zmk5566/Hexblocks/frontend/bridge/serial_bridge.py

#!/usr/bin/env python3
"""WearBlocks Serial-to-WebSocket bridge.

Reads $-prefixed lines from ESP32 hub serial, broadcasts JSON over WebSocket.

Usage:
  python serial_bridge.py /dev/cu.usbmodem14101   # real hardware
  python serial_bridge.py --mock                   # single IMU simulator
  python serial_bridge.py --sim                    # interactive multi-module simulator
  python serial_bridge.py --sim-demo               # auto-load demo (HR stacked on IMU)
"""
import argparse, asyncio, base64, copy, json, math, os, random, re, sys, time, threading
from collections import deque
from datetime import datetime
from functools import partial
from http.server import SimpleHTTPRequestHandler, HTTPServer
from pathlib import Path

import serial
import websockets

from wb_eca import ECAEngine, Act, ActionMode, CH, Action as EcaAction
from logger_profile import (
    MAX_SUBSCRIPTIONS as LOGGER_MAX_SUBSCRIPTIONS,
    MODES as LOGGER_MODES,
    RECORD_TYPES as LOGGER_RECORD_TYPES,
    default_config_rev as logger_default_config_rev,
    decode_profile as decode_logger_profile,
    encode_profile_base64,
)
from wb_protocol import parse_line as _parse_wire
import serial_io
from transport import (
    Transport, SerialTransport, BleTransport, ble_scan as ble_scan_devices,
)
from osc_forwarder import (
    OscForwarder, schema_to_default_mappings, load_channel_catalog,
)
from osc_ingress import OscIngress, ControlRequest

WS_PORT, HTTP_PORT, BAUD = 8765, 3000, 115200

PAIRED_DEVICES_PATH = Path(__file__).parent / "paired_devices.json"


def _load_paired() -> list[dict]:
    """Return list of {address, name, last_seen, auto_reconnect}."""
    try:
        if PAIRED_DEVICES_PATH.exists():
            data = json.loads(PAIRED_DEVICES_PATH.read_text())
            if isinstance(data, list):
                return data
    except Exception as e:
        print(f"[bridge] failed to load paired devices: {e!r}")
    return []


def _save_paired(devices: list[dict]) -> None:
    try:
        PAIRED_DEVICES_PATH.write_text(json.dumps(devices, indent=2))
    except Exception as e:
        print(f"[bridge] failed to save paired devices: {e!r}")


def _upsert_paired(address: str, name: str, *, auto_reconnect: bool | None = None):
    devs = _load_paired()
    now = int(time.time())
    found = None
    for d in devs:
        if d.get("address") == address:
            found = d
            break
    if found is None:
        found = {"address": address, "name": name,
                 "last_seen": now, "auto_reconnect": False}
        devs.append(found)
    else:
        found["name"] = name or found.get("name", "")
        found["last_seen"] = now
    if auto_reconnect is not None:
        found["auto_reconnect"] = bool(auto_reconnect)
    _save_paired(devs)
    return found


def _forget_paired(address: str) -> bool:
    devs = _load_paired()
    new = [d for d in devs if d.get("address") != address]
    if len(new) == len(devs):
        return False
    _save_paired(new)
    return True


# ── Debug recorder ───────────────────────────────────────────────
# When `--log <path>` is passed, every serial line in/out, every parsed
# event, and every WS-inbound command is appended to the file with an
# ISO timestamp and a one-letter direction tag:
#   RX  hub → bridge (raw serial line, with or without $)
#   TX  bridge → hub (write queue commands)
#   EV  parsed event broadcast to WS clients
#   WS  WS client → bridge inbound JSON
#   ..  bridge diagnostics (transport connect/drop, reset markers)
# Writes are flushed per line so an unclean shutdown still leaves a
# usable trail.
class LogRecorder:
    def __init__(self, path: str | None):
        self._fh = None
        if path:
            self._fh = open(path, "a", buffering=1, encoding="utf-8")
            self._write("--", f"--- bridge start pid={__import__('os').getpid()} ---")

    def _write(self, tag: str, text: str):
        if self._fh is None:
            return
        try:
            ts = datetime.now().isoformat(timespec="milliseconds")
            self._fh.write(f"{ts} {tag} {text}\n")
        except Exception:
            pass  # never let logging crash the bridge

    def rx(self, line: str):
        self._write("RX", line.rstrip("\r\n"))

    def tx(self, line: str):
        self._write("TX", line.rstrip("\r\n"))

    def event(self, msg: dict):
        try:
            self._write("EV", json.dumps(msg, ensure_ascii=False))
        except Exception:
            self._write("EV", repr(msg))

    def ws(self, raw: str):
        self._write("WS", raw if isinstance(raw, str) else repr(raw))

    def note(self, text: str):
        self._write("..", text)

    def close(self):
        if self._fh is not None:
            try:
                self._fh.close()
            except Exception:
                pass


recorder = LogRecorder(None)  # replaced in main() if --log given

HUB_RESET_MARKERS = (
    "WearBlocks Hub",
    "ESP-ROM",
    "rst:",
    "boot:",
    "Brownout",
    "Guru Meditation",
    "Rebooting",
)
HUB_READY_MARKERS = (
    "[WAIT] Listening for HELLO",
    "[WAIT] Listening for module HELLO",
)


def _classify_debug_line(line: str) -> str | None:
    """Return a compact diagnostic tag for notable hub debug output."""
    if any(marker in line for marker in HUB_RESET_MARKERS):
        return "hub_reset_marker"
    if any(marker in line for marker in HUB_READY_MARKERS):
        return "hub_ready_marker"
    return None

DEFAULT_MODULE_COLOR = "#888888"
COLOR_MAP = {
    "imu": "#7CA1BB", "imuv": "#7CA1BB",
    "motion_sensing": "#7CA1BB", "acc": "#7CA1BB",
    "acceleration": "#7CA1BB", "accelerometer": "#7CA1BB",
    "hr": "#7B68EE", "spo": "#7B68EE",
    "biometric": "#7B68EE", "heart": "#7B68EE",
    "tmp": "#F5A623", "temp": "#F5A623", "bme": "#F5A623",
    "environmental": "#F5A623",
    "vib": "#50C878", "vibration": "#50C878",
    "haptic": "#50C878", "haptic_output": "#50C878",
    "led": "#C68E9E", "visual_output": "#C68E9E",
    "rgb": "#C68E9E", "neopixel": "#C68E9E",
    "light": "#C1B496", "light_sensing": "#C1B496",
    "audio": "#9885BF", "audio_output": "#9885BF",
    "audio_synth": "#9885BF", "amp": "#9885BF",
    "amplifier": "#9885BF", "speaker": "#9885BF",
    "tone": "#9885BF", "tone_generation": "#9885BF",
    "tone_generator": "#9885BF",
    "wireless_uplink": "#4FA7A1", "logger": "#4FA7A1",
    "lora": "#4FA7A1", "loralog": "#4FA7A1",
    "lora_uplink": "#4FA7A1", "batch_log": "#4FA7A1",
    "motor": "#D97757", "dual_motor": "#D97757",
    "motor_output": "#D97757",
    "knob": "#98AF6F", "rotary": "#98AF6F",
    "input_control": "#98AF6F", "pot": "#98AF6F",
    "hub": "#989898",
}
COLOR_PREFIXES = (
    "imu", "acc", "hr", "spo", "tmp", "temp", "bme",
    "vib", "led", "light", "audio", "amp", "knob", "hub",
    "lora", "logger", "motor",
)

# Category → sensor type shorthand (for WebSocket "sensor" field)
CAT_MAP = {
    "motion_sensing": "imu",
    "biometric":      "hr",
    "environmental":  "temp",
    "visual_output":  "led",
    "haptic_output":  "vibration",
    "light_sensing":  "light",
    "audio_output":   "audio",
    "wireless_uplink": "logger",
    "motor_output":   "motor",
}

clients: set = set()

# ── Identity model ────────────────────────────────────────────────
# The hub's v2 wire protocol is UID-keyed: every $H/$D/$I/$S/$X/$U/$F/$C/$c/$T
# line carries the module's 8-hex-char UID. Slot is a hub-internal concept;
# it never appears on the wire after the v2 refactor. The bridge therefore
# keys all caches by UID. The sim modes (which still need slot for the ECA
# engine's action dispatch) keep their own slot-keyed bookkeeping via the
# uid_by_slot / slot_by_uid side indexes.

# UID-keyed caches (populated by parse_line from real hardware and, after
# commit 3, by the sim's synthetic-UID broadcast path).
modules_by_uid: dict = {}           # uid → mod_id
module_types_by_uid: dict = {}      # uid → sensor type shorthand
msg_cache_by_uid: dict = {}         # uid → {"hello": msg, "descriptor": msg}
link_cache_by_uid: dict = {}        # uid → latest link_state msg
# Stack relationships keyed by parent UID + face.
stack_cache_by_uid: dict = {}       # (parent_uid, parent_face) → child_stack msg
# Latest actuator state per uid (LED + vib).
actuator_cache_by_uid: dict = {}    # uid → actuator_state msg
logger_status_by_uid: dict = {}     # uid → latest logger_status msg
logger_config_by_uid: dict = {}     # uid → latest bridge-sent logger_config msg

# `$Q,DONE` is intentionally compact on the firmware wire, so the bridge tracks
# the outbound query commands that are known to terminate with DONE and annotates
# the inbound JSON event with `command`. This lets browser clients distinguish an
# empty TOPO snapshot from a STATUS/ECA completion with no topology rows.
QUERY_DONE_COMMANDS = {"STATUS", "TOPO", "ECA"}
pending_query_done_commands: deque[str] = deque()
topo_snapshot_uids: set[str] = set()
WIRELESS_TRANSPORT_MODES = {
    "can_only",
    "wifi_only",
    "can_primary_wifi_fallback",
    "wifi_primary_can_fallback",
    "dual_send_debug",
}

# Side indexes for sim / ECA dispatch — slot is CAN-bus addressing concept,
# not exposed on the v2 wire. Populated by sim in commit 3.
uid_by_slot: dict = {}              # slot → uid (sim authoritative)
slot_by_uid: dict = {}              # uid → slot (sim authoritative)

# Legacy slot-keyed caches — retained only so the existing sim path keeps
# working during this transitional commit. Commit 3 removes these by
# migrating the sim to emit uid-keyed frames via the _by_uid dicts above.
modules: dict = {}
module_types: dict = {}
msg_cache: dict = {}
stack_cache: dict = {}
actuator_cache: dict = {}

serial_write_queue: asyncio.Queue = asyncio.Queue()

# Request-ID-bearing OSC controls waiting for a Hub/simulator result. The
# actual UDP socket lives in ``osc_ingress``; keeping lifecycle state here lets
# normal parsed bridge events close the loop without coupling wb_protocol.py to
# networking.
osc_ingress: OscIngress | None = None
osc_control_pending: dict[str, dict] = {}
OSC_CONTROL_ROUTE_TIMEOUT_S = 3.0
OSC_CONTROL_RETENTION_S = 10.0

# ── Active transport (USB or BLE — mutually exclusive) ─────────
# Set by serial_loop / ble_loop. The transport_supervisor coroutine
# watches `transport_request` for switch commands from WS clients.
current_transport: Transport | None = None
transport_request: asyncio.Queue = asyncio.Queue()
# Cached for the next client that connects so the UI can render the
# current transport without a fresh status push.
last_transport_status: dict = {"type": "transport_status",
                                "transport": None, "address": None,
                                "label": None, "connected": False}

# Latest ECA status + bytecode from the hub. Cached so a freshly-
# connected WS client gets a full snapshot without waiting for the
# next $Q,ECA round-trip.
last_eca_status:   dict | None = None
last_eca_bytecode: dict | None = None


def clear_hub_runtime_state() -> None:
    """Discard identities and replay caches owned by a disconnected Hub."""
    global last_eca_status, last_eca_bytecode
    for cache in (
        modules_by_uid, module_types_by_uid, msg_cache_by_uid,
        stack_cache_by_uid, actuator_cache_by_uid,
        uid_by_slot, slot_by_uid,
        modules, module_types, msg_cache, stack_cache, actuator_cache,
    ):
        cache.clear()
    pending_query_done_commands.clear()
    topo_snapshot_uids.clear()
    last_eca_status = None
    last_eca_bytecode = None
    for request_id in list(osc_control_pending):
        if osc_ingress is not None:
            osc_ingress.result(request_id, ok=False, stage="transport",
                               detail="Hub transport disconnected")
        _finish_osc_control(request_id)

# ── ECA engine (used in --sim modes only) ──────────────────────
# Per-module-type mapping from simulator data field name → ECA channel id.
# Field names should match the channel catalog labels so legacy batched
# simulator payloads do not surface fake axis names in the frontend.
SIM_CHANNEL_MAP = {
    "imu":  {"ax": CH.AX, "ay": CH.AY, "az": CH.AZ,
             "gx": CH.GX, "gy": CH.GY, "gz": CH.GZ},
    "hr":   {"bpm": CH.BPM, "spo2": CH.SPO2},
    "temp": {"celsius": CH.CELSIUS, "humidity": CH.HUMIDITY},
    "knob": {"knob": CH.KNOB},
    "light": {"light": CH.LIGHT},
}


def _sim_monotonic_ms() -> int:
    """Monotonic clock for simulator scheduling; wall-clock jumps are irrelevant."""
    return time.monotonic_ns() // 1_000_000

# One global engine. The on_action callback is set later (after dispatch_action
# is defined) to avoid forward-reference noise.
eca = ECAEngine()

# Embedded OSC forwarder (Mode B: hub → bridge → UDP/OSC sink). Started in
# main() so it binds to the running asyncio loop. forward(msg) is called
# from broadcast(); see osc_forwarder.py for queue + drop-oldest design.
# `allow_remote` is patched in main() from the CLI flag before start().
osc_forwarder = OscForwarder()


async def _enqueue_osc_control(request: ControlRequest) -> None:
    osc_control_pending[request.request_id] = {
        "request": request,
        "queued_at": time.monotonic(),
        "routed_at": None,
        "state_seen": False,
    }
    await serial_write_queue.put(request.serial_line)
    print(f"[bridge] OSC→serial: $AO {request.request_id} "
          f"{request.uid} {request.cmd} (<{len(request.wire_params)} bytes>)")


def create_osc_ingress(
    host: str = "127.0.0.1",
    port: int = 7001,
    *,
    allow_remote: bool = False,
) -> OscIngress:
    """Create the OSC control listener on the shared command queue seam."""
    return OscIngress(
        host=host,
        port=port,
        allow_remote=allow_remote,
        known_uids=lambda: modules_by_uid.keys(),
        enqueue=_enqueue_osc_control,
        on_error=lambda message: print(f"[osc-in] rejected: {message}"),
    )


def _finish_osc_control(request_id: str) -> None:
    osc_control_pending.pop(request_id, None)
    if osc_ingress is not None:
        osc_ingress.forget(request_id)


def _handle_osc_bridge_event(msg: dict) -> None:
    """Translate normal bridge events into unicast OSC control replies."""
    if osc_ingress is None:
        return
    mtype = msg.get("type")

    if mtype == "command_ack":
        # Hub/sim replies: "$OK AO <request_id> ..." / "$ERR AO ...".
        match = re.match(r"^AO\s+([A-Za-z0-9_.:-]{1,64})(?:\s|$)",
                         str(msg.get("text", "")))
        if not match:
            return
        request_id = match.group(1)
        pending = osc_control_pending.get(request_id)
        if pending is None:
            return
        ok = msg.get("status") == "ok"
        osc_ingress.result(
            request_id, ok=ok, stage="routed" if ok else "route",
            detail=str(msg.get("text", "")))
        if ok:
            pending["routed_at"] = time.monotonic()
            if pending.get("state_seen") and "route=local" in str(msg.get("text", "")):
                osc_ingress.result(request_id, ok=True, stage="applied",
                                   detail="local actuator executed")
                _finish_osc_control(request_id)
        else:
            _finish_osc_control(request_id)
        return

    if mtype == "actuator_state":
        request_id = str(msg.get("request_id") or "")
        if not request_id or request_id not in osc_control_pending:
            return
        pending = osc_control_pending[request_id]
        pending["state_seen"] = True
        osc_ingress.state(request_id, msg)
        if msg.get("confirmed"):
            osc_ingress.result(request_id, ok=True, stage="applied",
                               detail="actuator state confirmed")
            _finish_osc_control(request_id)
        return

    if mtype == "wireless_command_result":
        request_id = str(msg.get("request_id") or "")
        if not request_id or request_id not in osc_control_pending:
            return
        ok = msg.get("status") == "ack"
        osc_ingress.result(
            request_id, ok=ok, stage="applied" if ok else "module",
            detail=str(msg.get("detail", "")))
        _finish_osc_control(request_id)


async def _osc_control_timeout_loop() -> None:
    while True:
        await asyncio.sleep(0.25)
        now = time.monotonic()
        for request_id, pending in list(osc_control_pending.items()):
            routed_at = pending.get("routed_at")
            if routed_at is None:
                if now - pending["queued_at"] >= OSC_CONTROL_ROUTE_TIMEOUT_S:
                    if osc_ingress is not None:
                        osc_ingress.result(request_id, ok=False, stage="route",
                                           detail="Hub response timeout")
                    _finish_osc_control(request_id)
            elif now - routed_at >= OSC_CONTROL_RETENTION_S:
                # CAN currently has no module-level action ACK. A routed ACK
                # plus commanded state is the strongest honest result there;
                # retain briefly for late state, then release bookkeeping.
                _finish_osc_control(request_id)


def _is_hex_color(value) -> bool:
    if not isinstance(value, str):
        return False
    value = value.strip()
    return (
        len(value) == 7
        and value.startswith("#")
        and all(ch in "0123456789abcdefABCDEF" for ch in value[1:])
    )


def _color_tokens(value):
    raw = str(value or "").strip().lower()
    if not raw:
        return
    normalized = re.sub(r"[^a-z0-9]+", "_", raw).strip("_")
    if not normalized:
        return
    yield normalized
    for part in normalized.split("_"):
        if not part:
            continue
        yield part
        prefix = re.match(r"[a-z]+", part)
        if prefix:
            yield prefix.group(0)


def _descriptor_color(desc: dict | None) -> str | None:
    if not isinstance(desc, dict):
        return None
    if _is_hex_color(desc.get("color")):
        return desc["color"].strip()
    signals = [
        desc.get("id"),
        desc.get("moduleId"),
        desc.get("name"),
        desc.get("type"),
        desc.get("cat"),
        desc.get("category"),
    ]
    for cap in desc.get("caps", []) or []:
        if not isinstance(cap, dict):
            continue
        signals.extend([
            cap.get("m"),
            cap.get("modality"),
            cap.get("t"),
            cap.get("type"),
        ])
    color = color_for(*signals)
    return None if color == DEFAULT_MODULE_COLOR else color


def color_for(*signals) -> str:
    for signal in signals:
        for token in _color_tokens(signal) or ():
            if token in COLOR_MAP:
                return COLOR_MAP[token]
            for prefix in COLOR_PREFIXES:
                if token.startswith(prefix):
                    return COLOR_MAP[prefix]
    return DEFAULT_MODULE_COLOR


def _descriptor_tokens(desc: dict | None) -> set[str]:
    tokens = set()

    def add(value):
        for token in _color_tokens(value) or ():
            tokens.add(token)

    if not isinstance(desc, dict):
        return tokens
    for key in ("id", "moduleId", "name", "type", "cat", "category"):
        add(desc.get(key))
    for cap in desc.get("caps", []) or []:
        if not isinstance(cap, dict):
            continue
        for key in ("t", "type", "m", "modality"):
            add(cap.get(key))
    return tokens


def _module_is_logger_uid(uid: str) -> bool:
    uid = str(uid or "").strip().upper()
    desc = msg_cache_by_uid.get(uid, {}).get("descriptor", {}).get("data")
    if not desc:
        slot = slot_by_uid.get(uid)
        sim_mod = sim_modules.get(slot) if slot is not None else None
        if sim_mod is not None:
            desc = sim_mod.descriptor
    tokens = _descriptor_tokens(desc)
    mod_id = modules_by_uid.get(uid, "")
    tokens.update(_color_tokens(mod_id) or [])
    return bool({
        "loralogv1", "loralog", "logger", "wireless_uplink",
        "lora_uplink", "batch_log",
    } & tokens)


def _catalog_channel_ids_for_type(sensor_type: str) -> set[int]:
    try:
        catalog = load_channel_catalog(CHANNEL_CATALOG_PATH)
    except Exception:
        return set()
    channels = catalog.get("channels", {})
    names = catalog.get("sensor_capabilities", {}).get(sensor_type, []) or []
    out = set()
    for name in names:
        entry = channels.get(name)
        if isinstance(entry, dict) and isinstance(entry.get("id"), int):
            out.add(int(entry["id"]))
    return out


def _channel_ids_for_uid(uid: str) -> set[int]:
    uid = str(uid or "").strip().upper()
    desc = msg_cache_by_uid.get(uid, {}).get("descriptor", {}).get("data")
    tokens = _descriptor_tokens(desc)
    sensor_type = module_types_by_uid.get(uid)
    if sensor_type:
        tokens.add(sensor_type)
    ids = set()
    for token in tokens:
        ids.update(_catalog_channel_ids_for_type(token))
    return ids


def _validate_logger_subscriptions(raw_subs, logger_uid: str) -> list[dict]:
    if not isinstance(raw_subs, list):
        raise ValueError("subscriptions must be a list")
    if len(raw_subs) > LOGGER_MAX_SUBSCRIPTIONS:
        raise ValueError(f"too many subscriptions, max {LOGGER_MAX_SUBSCRIPTIONS}")

    logger_uid = str(logger_uid or "").strip().upper()
    normalized: list[dict] = []
    seen = set()
    for raw in raw_subs:
        if not isinstance(raw, dict):
            raise ValueError("subscription must be an object")
        sub = {
            "source_uid": str(raw.get("source_uid", "")).strip().upper().replace("0X", ""),
            "channel_id": int(raw.get("channel_id", 0)),
            "record_type": str(raw.get("record_type", "sensor")).strip(),
            "mode": str(raw.get("mode", "latest_interval")).strip(),
            "min_interval_ms": int(raw.get("min_interval_ms", 0)),
            "threshold": float(raw.get("threshold", 0.0)),
            "flags": int(raw.get("flags", 0)),
        }
        if sub["record_type"] not in LOGGER_RECORD_TYPES:
            raise ValueError(f"bad record_type {sub['record_type']!r}")
        if sub["mode"] not in LOGGER_MODES:
            raise ValueError(f"bad logger mode {sub['mode']!r}")
        if not re.fullmatch(r"[0-9A-F]{8}", sub["source_uid"]):
            raise ValueError(f"bad source_uid {sub['source_uid']!r}")
        if sub["source_uid"] == logger_uid:
            raise ValueError("logger cannot subscribe to itself")
        if sub["source_uid"] not in modules_by_uid:
            raise ValueError(f"unknown source_uid {sub['source_uid']}")
        if not 0 <= sub["channel_id"] < 48:
            raise ValueError("channel_id must be 0..47")
        if not 0 <= sub["min_interval_ms"] <= 86_400_000:
            raise ValueError("min_interval_ms out of range")
        if not math.isfinite(sub["threshold"]):
            raise ValueError("threshold must be finite")
        if not 0 <= sub["flags"] <= 255:
            raise ValueError("flags must be 0..255")
        if sub["record_type"] == "sensor":
            allowed = _channel_ids_for_uid(sub["source_uid"])
            if allowed and sub["channel_id"] not in allowed:
                raise ValueError(
                    f"channel {sub['channel_id']} is not advertised by {sub['source_uid']}"
                )
        key = (sub["source_uid"], sub["channel_id"], sub["record_type"])
        if key in seen:
            continue
        seen.add(key)
        normalized.append(sub)
    return normalized


def _track_query_command(command: str) -> None:
    cmd = str(command or "").strip().upper()
    if cmd in QUERY_DONE_COMMANDS:
        pending_query_done_commands.append(cmd)


def _clear_pending_query_state(reason: str) -> None:
    pending = len(pending_query_done_commands)
    topo_rows = len(topo_snapshot_uids)
    if not pending and not topo_rows:
        return
    pending_query_done_commands.clear()
    topo_snapshot_uids.clear()
    recorder.note(
        f"cleared pending query state ({pending} done marker(s), "
        f"{topo_rows} topo row(s)): {reason}"
    )


async def _queue_query_command(command: str) -> None:
    """Queue a hub query and remember which compact $Q,DONE it will finish."""
    cmd = str(command or "").strip().upper()
    if not cmd:
        return
    _track_query_command(cmd)
    await serial_write_queue.put(f"$Q,{cmd}\n")


def _drop_pending_query_writes(reason: str) -> int:
    """Remove stale queued $Q commands before a newly opened transport sync."""
    kept = []
    dropped = 0
    while True:
        try:
            cmd = serial_write_queue.get_nowait()
        except asyncio.QueueEmpty:
            break
        if str(cmd).lstrip().upper().startswith("$Q,"):
            dropped += 1
        else:
            kept.append(cmd)
    for cmd in kept:
        serial_write_queue.put_nowait(cmd)
    if dropped:
        _clear_pending_query_state(reason)
        recorder.note(f"dropped {dropped} queued query command(s): {reason}")
        print(f"[bridge] dropped {dropped} queued query command(s): {reason}")
    else:
        _clear_pending_query_state(reason)
    return dropped


def _consume_tracked_query_done(command: str) -> None:
    cmd = str(command or "").strip().upper()
    if pending_query_done_commands and pending_query_done_commands[0] == cmd:
        pending_query_done_commands.popleft()


def _prune_uid_caches_to(live_uids: set[str]) -> None:
    """Drop bridge replay caches for UIDs absent from an authoritative TOPO."""
    cached_uids = (set(modules_by_uid) | set(module_types_by_uid)
                   | set(msg_cache_by_uid) | set(link_cache_by_uid)
                   | set(actuator_cache_by_uid)
                   | set(logger_status_by_uid) | set(logger_config_by_uid)
                   | set(slot_by_uid))
    dead_uids = cached_uids - live_uids
    for uid in dead_uids:
        modules_by_uid.pop(uid, None)
        module_types_by_uid.pop(uid, None)
        msg_cache_by_uid.pop(uid, None)
        link_cache_by_uid.pop(uid, None)
        actuator_cache_by_uid.pop(uid, None)
        logger_status_by_uid.pop(uid, None)
        logger_config_by_uid.pop(uid, None)
        slot = slot_by_uid.pop(uid, None)
        if slot is not None:
            uid_by_slot.pop(slot, None)

    for key, stack_msg in list(stack_cache_by_uid.items()):
        parent_uid, _parent_face = key
        child_uid = stack_msg.get("child_uid")
        if parent_uid not in live_uids or (child_uid and child_uid not in live_uids):
            stack_cache_by_uid.pop(key, None)

    if dead_uids:
        print(f"[bridge] TOPO pruned stale cache: {sorted(dead_uids)}")


def _wire_u32_be(params: list[int], offset: int) -> int:
    if len(params) < offset + 4:
        return 0
    return ((params[offset] << 24) | (params[offset + 1] << 16)
            | (params[offset + 2] << 8) | params[offset + 3])


def _decode_wire_actuator_state(msg: dict) -> dict:
    """Project a Hub $AS command echo into the UI's rich actuator shape."""
    uid = msg["uid"]
    command = int(msg.get("cmd", 0))
    params = [int(value) & 0xFF for value in msg.get("params", [])]
    previous = actuator_cache_by_uid.get(uid, {})
    now_ms = int(time.time() * 1000)
    state = {
        **previous,
        **msg,
        "uid": uid,
        "slot": slot_by_uid.get(uid),
        "cmd": command,
        "params": params,
        "ts": now_ms,
        "led": copy.deepcopy(previous.get("led", {
            "r": 0, "g": 0, "b": 0, "brightness": 0,
            "mode": "off", "until_ms": 0,
        })),
        "vib": copy.deepcopy(previous.get("vib", {
            "intensity": 0, "mode": "off", "until_ms": 0,
        })),
        "audio": copy.deepcopy(previous.get("audio", {
            "frequency_hz": 0, "amplitude": 0, "mode": "off",
            "until_ms": 0,
        })),
        "motors": copy.deepcopy(previous.get("motors", {
            "1": {"mode": "stop", "speed": 0, "until_ms": 0},
            "2": {"mode": "stop", "speed": 0, "until_ms": 0},
        })),
    }

    if command in (Act.LED_OFF, Act.LED_STOP):
        state["led"] = {"r": 0, "g": 0, "b": 0, "brightness": 0,
                        "mode": "off", "until_ms": 0}
    elif command in (Act.LED_SOLID, Act.LED_RAMP, Act.LED_BREATHE,
                     Act.LED_BLINK, Act.LED_RAINBOW):
        duration = _wire_u32_be(params, 3)
        state["led"] = {
            "r": params[0] if len(params) > 0 else 0,
            "g": params[1] if len(params) > 1 else 0,
            "b": params[2] if len(params) > 2 else 0,
            "brightness": 255,
            "mode": "solid" if command == Act.LED_SOLID else "effect",
            "until_ms": now_ms + duration if duration else 0,
        }
    elif command == Act.VIBRATE:
        duration = _wire_u32_be(params, 1)
        state["vib"] = {
            "intensity": params[0] if params else 0,
            "mode": "on",
            "until_ms": now_ms + duration if duration else 0,
        }
    elif command == Act.VIBRATE_PULSE:
        on_ms = (params[1] if len(params) > 1 else 10) * 10
        off_ms = (params[2] if len(params) > 2 else 10) * 10
        count = params[3] if len(params) > 3 else 1
        duration = (on_ms + off_ms) * max(1, count)
        state["vib"] = {
            "intensity": params[0] if params else 0,
            "mode": "pulse", "on_ms": on_ms, "off_ms": off_ms,
            "count": count, "until_ms": now_ms + duration,
        }
    elif command == Act.VIBRATE_RAMP:
        duration = _wire_u32_be(params, 2)
        state["vib"] = {
            "intensity": params[1] if len(params) > 1 else 0,
            "from": params[0] if params else 0,
            "mode": "ramp",
            "until_ms": now_ms + duration if duration else 0,
        }
    elif command == Act.VIBRATE_STOP:
        state["vib"] = {"intensity": 0, "mode": "off", "until_ms": 0}
    elif command == Act.AUDIO_SET_TONE:
        frequency = (params[0] if params else 0) \
            | ((params[1] if len(params) > 1 else 0) << 8)
        duration = _wire_u32_be(params, 3)
        state["audio"] = {
            "frequency_hz": frequency,
            "amplitude": params[2] if len(params) > 2 else 0,
            "mode": "tone",
            "until_ms": now_ms + duration if duration else 0,
        }
    elif command == Act.AUDIO_STOP:
        state["audio"] = {"frequency_hz": 0, "amplitude": 0,
                          "mode": "off", "until_ms": 0}
    elif command == Act.MOTOR_SET and len(params) >= 5:
        motor = params[0]
        mode = params[1]
        duration = (params[3] << 8) | params[4]
        if motor in (1, 2):
            state["motors"][str(motor)] = {
                "mode": ("stop" if mode == 0 or params[2] == 0 else
                         "forward" if mode == 1 else "reverse"),
                "speed": params[2],
                "until_ms": now_ms + duration if duration else 0,
            }
    return state


def parse_line(raw: str):
    """Parse a $-prefixed hub line into the bridge's JSON-shaped event.

    Wire decoding is delegated to `wb_protocol.parse_line`; this wrapper
    adds bridge-layer concerns: slot crosswalk via `slot_by_uid`, color
    derivation, descriptor field normalization, the `face` back-compat
    alias, and the cache cleanup triggered by `$U`.
    """
    msg = _parse_wire(raw)
    if msg is None:
        return None
    mtype = msg["type"]

    if mtype == "hello":
        uid = msg["uid"]
        if msg["id"]:
            modules_by_uid[uid] = msg["id"]
        mod_id = msg["id"] or modules_by_uid.get(uid, "")
        cached_desc = msg_cache_by_uid.get(uid, {}).get("descriptor", {}).get("data")
        msg["id"] = mod_id
        msg["slot"] = slot_by_uid.get(uid)
        msg["color"] = _descriptor_color(cached_desc) \
            or color_for(mod_id, module_types_by_uid.get(uid))
        # Legacy `face` alias is the *hub* face the module sits on, or 0
        # for a stacked child (which has no hub face — its position is
        # described by parent_uid + parent_face, not by its own face).
        # Setting face=parent_face unconditionally would make the canvas
        # draw stacked children at hub.F<parent_face> for the brief
        # window between cache replay and TOPO reconcile, which looks
        # exactly like an orphan module.
        msg["face"] = msg["parent_face"] if msg["parent_is_hub"] else 0
        cached_link = link_cache_by_uid.get(uid)
        if cached_link:
            msg["active_link"] = cached_link.get("active_link")
            msg["transport_mode"] = cached_link.get("transport_mode")
            msg["topology_state"] = cached_link.get("topology_state")
        return msg

    if mtype == "descriptor":
        uid = msg["uid"]
        desc = dict(msg["data"])
        if "type" not in desc:
            cat = desc.get("cat", "")
            desc["type"] = CAT_MAP.get(cat, cat)
            caps = desc.get("caps", [])
            if caps and not desc["type"]:
                desc["type"] = caps[0].get("m", "unknown")
        if "name" not in desc and "nm" in desc:
            desc["name"] = desc["nm"]
        if "version" not in desc and "ver" in desc:
            desc["version"] = desc["ver"]
        if "rate" not in desc:
            caps = desc.get("caps", [])
            if caps:
                sr = caps[0].get("sr", [])
                desc["rate"] = sr[0] if sr else 0
        derived_color = _descriptor_color(desc)
        if derived_color:
            desc["color"] = derived_color
        module_types_by_uid[uid] = desc.get("type", "imu")
        msg["data"] = desc
        msg["slot"] = slot_by_uid.get(uid)
        return msg

    if mtype == "module_info":
        uid = msg["uid"]
        if msg["id"]:
            modules_by_uid[uid] = msg["id"]
        cached_desc = msg_cache_by_uid.get(uid, {}).get("descriptor", {}).get("data")
        msg["slot"] = slot_by_uid.get(uid)
        msg["color"] = _descriptor_color(cached_desc) \
            or color_for(msg["id"], modules_by_uid.get(uid), module_types_by_uid.get(uid))
        return msg

    if mtype == "sensor":
        uid = msg["uid"]
        msg["sensor"] = module_types_by_uid.get(uid, "imu")
        msg["slot"] = slot_by_uid.get(uid)
        msg["ts"] = int(time.time() * 1000)
        return msg

    if mtype == "detach_pending":
        msg["slot"] = slot_by_uid.get(msg["uid"])
        return msg

    if mtype == "unplug":
        uid = msg["uid"]
        modules_by_uid.pop(uid, None)
        module_types_by_uid.pop(uid, None)
        msg_cache_by_uid.pop(uid, None)
        actuator_cache_by_uid.pop(uid, None)
        dead_keys = [k for k in stack_cache_by_uid if k[0] == uid]
        for k in dead_keys:
            stack_cache_by_uid.pop(k, None)
        slot = slot_by_uid.pop(uid, None)
        if slot is not None:
            uid_by_slot.pop(slot, None)
        msg["slot"] = slot
        return msg

    if mtype == "face_swap":
        msg["slot"] = slot_by_uid.get(msg["uid"])
        return msg

    if mtype == "topology":
        msg["slot"] = slot_by_uid.get(msg["uid"])
        topo_snapshot_uids.add(msg["uid"])
        return msg

    if mtype == "link_state":
        uid = msg["uid"]
        msg["slot"] = slot_by_uid.get(uid)
        link_cache_by_uid[uid] = dict(msg)
        cached = msg_cache_by_uid.get(uid, {}).get("hello")
        if cached:
            cached["active_link"] = msg.get("active_link")
            cached["transport_mode"] = msg.get("transport_mode")
            cached["topology_state"] = msg.get("topology_state")
        return msg

    if mtype == "actuator_state":
        uid = msg["uid"]
        msg["slot"] = slot_by_uid.get(uid)
        return _decode_wire_actuator_state(msg)

    if mtype == "wireless_command_result":
        msg["slot"] = slot_by_uid.get(msg["uid"])
        return msg

    if mtype == "logger_status":
        uid = msg["uid"]
        msg["slot"] = slot_by_uid.get(uid)
        return msg

    if mtype == "query_done":
        cmd = pending_query_done_commands.popleft() if pending_query_done_commands else None
        # Back-compat for manually typed `$Q,TOPO` on the serial console or old
        # paths that did not call _track_query_command(): if topology rows were
        # just seen, the DONE must belong to that snapshot.
        if cmd is None and topo_snapshot_uids:
            cmd = "TOPO"
        if cmd:
            msg["command"] = cmd
        if cmd == "TOPO":
            _prune_uid_caches_to(set(topo_snapshot_uids))
        topo_snapshot_uids.clear()
        return msg

    # child_stack, child_unstack, command_ack, wifi_ap/pass/token/disabled:
    # pass through unchanged.
    return msg


def cache_msg(msg: dict):
    """Cache replayable module/logger messages for new clients.

    Real-hardware child_stack/child_unstack messages don't carry a top-level
    `uid` (only `parent_uid`/`child_uid`), so they're routed by parent_uid
    rather than uid. hello/descriptor/module_info/actuator_state are routed by uid;
    legacy slot-keyed sim variants (parent_slot/slot) are honoured as a
    fallback for older sim builds that haven't been migrated yet."""
    mtype = msg["type"]

    # Stack relationships — key by parent identity, not message uid.
    if mtype == "child_stack":
        parent_uid = msg.get("parent_uid")
        parent_face = msg.get("parent_face")
        if parent_uid and parent_face is not None:
            # Cache resolved links only (child_uid non-null / not pending).
            if not msg.get("pending"):
                stack_cache_by_uid[(parent_uid, parent_face)] = msg
        elif "parent_slot" in msg and "parent_face" in msg:
            if msg.get("child_slot", -1) >= 0:
                stack_cache[(msg["parent_slot"], msg["parent_face"])] = msg
        return

    if mtype == "child_unstack":
        parent_uid = msg.get("parent_uid")
        parent_face = msg.get("parent_face")
        if parent_uid and parent_face is not None:
            stack_cache_by_uid.pop((parent_uid, parent_face), None)
        elif "parent_slot" in msg and "parent_face" in msg:
            stack_cache.pop((msg["parent_slot"], msg["parent_face"]), None)
        return

    uid = msg.get("uid")
    if uid:
        if mtype == "hello":
            msg_cache_by_uid.setdefault(uid, {})["hello"] = msg
        elif mtype == "descriptor":
            msg_cache_by_uid.setdefault(uid, {})["descriptor"] = msg
        elif mtype == "module_info":
            msg_cache_by_uid.setdefault(uid, {})["module_info"] = msg
        elif mtype == "link_state":
            msg_cache_by_uid.setdefault(uid, {})["link_state"] = msg
            link_cache_by_uid[uid] = dict(msg)
        elif mtype == "actuator_state":
            actuator_cache_by_uid[uid] = msg
        elif mtype == "logger_status":
            logger_status_by_uid[uid] = msg
        elif mtype == "logger_config":
            logger_config_by_uid[uid] = msg
        return

    # Legacy slot-keyed sim path (hello/descriptor/actuator only — stack
    # variants handled above).
    slot = msg.get("slot")
    if slot is None:
        return
    if mtype == "hello":
        msg_cache.setdefault(slot, {})["hello"] = msg
    elif mtype == "descriptor":
        msg_cache.setdefault(slot, {})["descriptor"] = msg
    elif mtype == "actuator_state":
        actuator_cache[slot] = msg


async def broadcast(msg: dict):
    _handle_osc_bridge_event(msg)
    if msg["type"] in ("hello", "descriptor", "module_info", "link_state", "child_stack",
                       "child_unstack", "actuator_state", "logger_status",
                       "logger_config"):
        try:
            cache_msg(msg)
        except Exception as e:
            # A malformed message should never bring the serial loop down.
            # Log loudly and keep going so the WS clients still get the
            # event (and so the next valid line still reaches the bridge).
            print(f"[bridge] cache_msg failed for {msg.get('type')}: "
                  f"{e!r}; msg keys={list(msg.keys())}")
    elif msg["type"] == "eca_status":
        global last_eca_status
        last_eca_status = msg
    elif msg["type"] == "eca_bytecode":
        global last_eca_bytecode
        last_eca_bytecode = msg
    recorder.event(msg)
    payload = json.dumps(msg)
    dead = set()
    for ws in tuple(clients):
        try:
            await ws.send(payload)
        except websockets.exceptions.ConnectionClosed:
            dead.add(ws)
    clients.difference_update(dead)
    # Mode B fan-out: synchronous, non-blocking, drops oldest on overflow.
    # Only sensor + actuator_state are forwardable; other types are filtered
    # inside forward() so the cost here stays O(targets).
    osc_forwarder.forward(msg)


def _parse_line_selftest() -> None:
    """Assert the bridge's parse_line wrapper adds slot crosswalk, color,
    descriptor normalization, the `face` alias, and runs $U cleanup. Wire
    decoding is covered by `wb_protocol._selftest`, which we invoke first."""
    from wb_protocol import _selftest as _wire_selftest
    _wire_selftest()

    def clear_state():
        for d in (modules_by_uid, module_types_by_uid, msg_cache_by_uid,
                  stack_cache_by_uid, actuator_cache_by_uid,
                  logger_status_by_uid, logger_config_by_uid,
                  uid_by_slot, slot_by_uid):
            d.clear()
        pending_query_done_commands.clear()
        topo_snapshot_uids.clear()

    clear_state()
    # Pre-seed slot crosswalk so we can verify enrichment.
    uid_by_slot[3] = "A1B2C3D4"
    slot_by_uid["A1B2C3D4"] = 3

    h = parse_line("$H,A1B2C3D4,imuv2,HUB,1")
    assert h["slot"] == 3 and h["face"] == 1 \
        and h["color"] == "#7CA1BB" and h["id"] == "imuv2", h
    # Orphan $H recalls the cached module-id.
    assert parse_line("$H,A1B2C3D4,,HUB,1")["id"] == "imuv2"

    d = parse_line('$D,A1B2C3D4,{"id":"imuv2","nm":"IMU","cat":"motion_sensing","caps":[{"m":"acceleration","ax":3,"sr":[50]}]}')
    assert d["data"]["type"] == "imu" and d["data"]["name"] == "IMU" \
        and d["data"]["rate"] == 50 and d["slot"] == 3, d
    assert module_types_by_uid["A1B2C3D4"] == "imu"

    i = parse_line("$I,A1B2C3D4,imuv2,3.1,8F0A")
    assert i["slot"] == 3 and i["version"] == "3.1" \
        and i["fw_hash"] == "8F0A" and i["color"] == "#7CA1BB", i
    assert color_for("amp_009B7750") == "#9885BF"
    assert color_for("audiov1") == "#9885BF"
    assert _descriptor_color({
        "id": "custom_sound",
        "cat": "audio_output",
        "caps": [{"m": "audio_synth"}],
    }) == "#9885BF"
    lgd = parse_line('$D,FACE0010,{"id":"loralogv1","name":"LoRa Logger","cat":"wireless_uplink","caps":[{"t":"logger","m":"batch_log"}]}')
    cache_msg(lgd)
    assert _module_is_logger_uid("FACE0010")
    lgs = parse_line("$L,FACE0010,3,2,123,-88,6.25,1,99")
    assert (lgs["type"] == "logger_status" and lgs["slot"] is None
            and lgs["queue_depth"] == 3 and lgs["config_rev"] == 99), lgs

    s = parse_line("$S,A1B2C3D4,5,0.1234")
    assert s["sensor"] == "imu" and s["slot"] == 3 and "ts" in s, s

    u = parse_line("$U,A1B2C3D4")
    assert u["slot"] == 3
    assert "A1B2C3D4" not in modules_by_uid  # cleanup ran
    assert 3 not in uid_by_slot                # crosswalk torn down
    assert "A1B2C3D4" not in slot_by_uid

    # Resolve-target back-compat: slot → uid via side index.
    uid_by_slot[7] = "FEEDBEEF"
    assert _resolve_target({"uid": "ABC"}) == "ABC"
    assert _resolve_target({"slot": 7}) == "FEEDBEEF"
    assert _resolve_target({"slot": 99}) is None
    assert _resolve_target({}) is None

    # DONE is annotated with the tracked query command, and an authoritative
    # TOPO completion prunes stale replay caches for future WS clients.
    clear_state()
    modules_by_uid["FEEDBEEF"] = "imuv2"
    modules_by_uid["DEADCAFE"] = "ledv3"
    msg_cache_by_uid["DEADCAFE"] = {"hello": {"type": "hello", "uid": "DEADCAFE"}}
    _track_query_command("TOPO")
    t = parse_line("$T,FEEDBEEF,HUB,2")
    assert t["type"] == "topology" and t["uid"] == "FEEDBEEF"
    done = parse_line("$Q,DONE")
    assert done == {"type": "query_done", "command": "TOPO"}, done
    assert set(modules_by_uid) == {"FEEDBEEF"}
    assert "DEADCAFE" not in msg_cache_by_uid

    clear_state()
    _track_query_command("STATUS")
    assert parse_line("$Q,DONE") == {"type": "query_done", "command": "STATUS"}

    clear_state()
    print("[bridge] parse_line self-test OK")


async def ws_handler(ws):
    clients.add(ws)
    total_modules = len(modules_by_uid) + len(modules)
    await ws.send(json.dumps({"type": "status", "connected": True,
                               "modules": total_modules}))
    # Replay current transport state so the UI can render it immediately.
    if last_transport_status.get("transport") is not None or \
       last_transport_status.get("connected"):
        await ws.send(json.dumps(last_transport_status))
    # Replay paired-devices list so the Connections panel can render it
    # without an extra round-trip.
    await ws.send(json.dumps({"type": "paired_devices",
                               "devices": _load_paired()}))
    # Replay currently visible USB serial ports so the Connections panel can
    # offer a connection choice when the bridge was started with --idle.
    await ws.send(json.dumps({"type": "serial_ports",
                               "ports": serial_io.find_ports()}))
    # Replay current OSC target list so the panel renders without
    # an explicit osc_list round-trip.
    await ws.send(json.dumps({"type": "osc_state",
                               "targets": osc_forwarder.snapshot()}))
    # Replay last-known ECA snapshot so a reconnecting client can render
    # "what's running" immediately, even before the next $Q,ECA fires.
    if last_eca_status is not None:
        await ws.send(json.dumps(last_eca_status))
    if last_eca_bytecode is not None:
        await ws.send(json.dumps(last_eca_bytecode))
    # Replay UID-keyed caches first (real-hardware and, after commit 3, sim).
    for uid in sorted(msg_cache_by_uid):
        cached = msg_cache_by_uid[uid]
        if "hello" in cached:
            await ws.send(json.dumps(cached["hello"]))
        if "module_info" in cached:
            await ws.send(json.dumps(cached["module_info"]))
        if "link_state" in cached:
            await ws.send(json.dumps(cached["link_state"]))
        if "descriptor" in cached:
            await ws.send(json.dumps(cached["descriptor"]))
    for stack_msg in stack_cache_by_uid.values():
        await ws.send(json.dumps(stack_msg))
    for act_msg in actuator_cache_by_uid.values():
        await ws.send(json.dumps(act_msg))
    for status_msg in logger_status_by_uid.values():
        await ws.send(json.dumps(status_msg))
    for config_msg in logger_config_by_uid.values():
        await ws.send(json.dumps(config_msg))
    # Legacy slot-keyed replay — currently populated only by the sim path.
    for slot in sorted(msg_cache):
        cached = msg_cache[slot]
        if "hello" in cached:
            await ws.send(json.dumps(cached["hello"]))
        if "descriptor" in cached:
            await ws.send(json.dumps(cached["descriptor"]))
    for stack_msg in stack_cache.values():
        await ws.send(json.dumps(stack_msg))
    for act_msg in actuator_cache.values():
        await ws.send(json.dumps(act_msg))
    try:
        async for raw in ws:
            recorder.ws(raw)
            try:
                inbound = json.loads(raw)
                action = inbound.get("action")
                if action == "query":
                    cmd = str(inbound.get("command", "")).strip().upper()
                    if cmd == "DISCOVER":
                        print("[bridge] WS query ignored: $Q,DISCOVER is not implemented by firmware")
                        continue
                    if current_transport is None or not current_transport.is_open:
                        print(f"[bridge] WS query ignored (no active transport): $Q,{cmd}")
                        continue
                    await _queue_query_command(cmd)
                    print(f"[bridge] WS→serial: $Q,{cmd}")
                elif action == "program":
                    # Upload + auto-run an ECA bytecode program (base64).
                    b64 = inbound.get("data", "")
                    await serial_write_queue.put(f"$P {b64}\n")
                    print(f"[bridge] WS→serial: $P (<{len(b64)} chars>)")
                elif action == "program_run":
                    await serial_write_queue.put("$PR\n")
                elif action == "program_stop":
                    await serial_write_queue.put("$PS\n")
                elif action == "program_clear":
                    await serial_write_queue.put("$PC\n")
                elif action == "program_erase_nvs":
                    # Hub keeps the program running this session but won't
                    # auto-restore on next boot. See $PE in hub.ino.
                    await serial_write_queue.put("$PE\n")
                elif action == "actuator":
                    target = _resolve_target(inbound)
                    if target is None:
                        print(f"[bridge] actuator: no uid/slot in {inbound}")
                        continue
                    cmd  = int(inbound.get("cmd", 0))
                    params = inbound.get("params", []) or []
                    parts = " ".join(str(int(p)) for p in params)
                    line = f"$A {target} {cmd}" + (f" {parts}" if parts else "")
                    await serial_write_queue.put(line + "\n")
                    print(f"[bridge] WS→serial: {line}")
                elif action == "topic_enable":
                    target = _resolve_target(inbound)
                    if target is None: continue
                    ch   = int(inbound.get("channel", 0))
                    await serial_write_queue.put(f"$TE {target} {ch}\n")
                elif action == "topic_disable":
                    target = _resolve_target(inbound)
                    if target is None: continue
                    ch   = int(inbound.get("channel", 0))
                    await serial_write_queue.put(f"$TD {target} {ch}\n")
                elif action == "topic_enable_all":
                    target = _resolve_target(inbound)
                    if target is None: continue
                    await serial_write_queue.put(f"$TA {target}\n")
                elif action == "wireless_info":
                    await serial_write_queue.put("$W,INFO\n")
                    print("[bridge] WS→serial: $W,INFO")
                elif action == "wireless_config":
                    mode = str(inbound.get("mode", "")).strip()
                    if mode not in WIRELESS_TRANSPORT_MODES:
                        print(f"[bridge] wireless_config: bad mode {mode!r}")
                        continue
                    target = str(inbound.get("target", "")).strip().upper()
                    if target != "ALL":
                        resolved = _resolve_target(inbound)
                        target = str(resolved).strip().upper() if resolved else target
                    if target != "ALL" and not re.fullmatch(r"[0-9A-F]{8}", target):
                        print(f"[bridge] wireless_config: bad target {target!r}")
                        continue
                    line = f"$W,CONFIG {target} {mode}"
                    await serial_write_queue.put(line + "\n")
                    print(f"[bridge] WS→serial: {line}")
                elif action == "logger_info":
                    await serial_write_queue.put("$L,INFO\n")
                    print("[bridge] WS→serial: $L,INFO")
                elif action == "logger_config":
                    target = _resolve_target(inbound)
                    target = str(target or inbound.get("target", "")).strip().upper()
                    if not re.fullmatch(r"[0-9A-F]{8}", target):
                        await ws.send(json.dumps({
                            "type": "logger_error",
                            "text": "logger_config bad target",
                        }))
                        print(f"[bridge] logger_config: bad target {target!r}")
                        continue
                    if target not in modules_by_uid or not _module_is_logger_uid(target):
                        await ws.send(json.dumps({
                            "type": "logger_error",
                            "text": "target is not a logger module",
                        }))
                        print(f"[bridge] logger_config: target not logger {target!r}")
                        continue
                    try:
                        subs = _validate_logger_subscriptions(
                            inbound.get("subscriptions", []), target)
                        config_rev = int(inbound.get(
                            "config_rev", logger_default_config_rev()))
                        b64, decoded = encode_profile_base64(
                            subs, config_rev=config_rev)
                    except Exception as e:
                        await ws.send(json.dumps({
                            "type": "logger_error",
                            "text": str(e),
                        }))
                        print(f"[bridge] logger_config: {e}")
                        continue
                    line = f"$L,CONFIG {target} {b64}"
                    await serial_write_queue.put(line + "\n")
                    cfg_msg = {
                        "type": "logger_config",
                        "uid": target,
                        "slot": slot_by_uid.get(target),
                        "config_rev": decoded["config_rev"],
                        "subscriptions": decoded["subscriptions"],
                    }
                    await broadcast(cfg_msg)
                    print(f"[bridge] WS→serial: $L,CONFIG {target} "
                          f"(<{len(b64)} chars>, {len(subs)} subs)")
                elif action == "sim_command":
                    # Browser-side preset buttons (D1-D4, clear, etc.)
                    # in --sim modes only. Silently no-op when not in sim.
                    sim_cmd = str(inbound.get("command", "")).strip()
                    if sim_cmd_queue is not None and sim_cmd:
                        await sim_cmd_queue.put(sim_cmd)
                        print(f"[bridge] WS→sim: {sim_cmd}")
                elif action == "ble_scan":
                    duration = float(inbound.get("duration", 5))
                    asyncio.create_task(_run_ble_scan(duration))
                elif action == "serial_list":
                    await ws.send(json.dumps({"type": "serial_ports",
                                               "ports": serial_io.find_ports()}))
                elif action == "ble_connect":
                    addr = str(inbound.get("address", "")).strip()
                    name = str(inbound.get("name", "")).strip() or addr
                    if addr:
                        _upsert_paired(addr, name)
                        await transport_request.put(("ble", addr, name))
                        await broadcast({"type": "paired_devices",
                                          "devices": _load_paired()})
                elif action in ("ble_disconnect", "transport_disconnect"):
                    await transport_request.put(("none",))
                elif action == "ble_forget":
                    addr = str(inbound.get("address", "")).strip()
                    if addr and _forget_paired(addr):
                        await broadcast({"type": "paired_devices",
                                          "devices": _load_paired()})
                elif action == "ble_set_auto_reconnect":
                    addr = str(inbound.get("address", "")).strip()
                    enable = bool(inbound.get("enable", False))
                    if addr:
                        # When turning one on, turn the others off — at most
                        # one device should auto-reconnect.
                        if enable:
                            for d in _load_paired():
                                if d.get("address") != addr and d.get("auto_reconnect"):
                                    _upsert_paired(d["address"], d.get("name", ""),
                                                    auto_reconnect=False)
                        _upsert_paired(addr, inbound.get("name", "") or addr,
                                        auto_reconnect=enable)
                        await broadcast({"type": "paired_devices",
                                          "devices": _load_paired()})
                elif action == "transport_use_serial":
                    port = str(inbound.get("port", "")).strip()
                    if not port:
                        candidates = serial_io.find_ports()
                        port = candidates[0] if candidates else ""
                    if port:
                        await transport_request.put(("serial", port))
                elif action == "osc_list":
                    await ws.send(json.dumps({"type": "osc_state",
                                               "targets": osc_forwarder.snapshot()}))
                elif action == "osc_add":
                    tgt = inbound.get("target") or {}
                    if "host" in tgt and "port" in tgt:
                        added, err = osc_forwarder.add(tgt)
                        if err is not None:
                            await ws.send(json.dumps({"type": "osc_error",
                                                       "action": "add",
                                                       "error": err}))
                        else:
                            await broadcast({"type": "osc_state",
                                              "targets": osc_forwarder.snapshot()})
                elif action == "osc_update":
                    tid = str(inbound.get("id", "")).strip()
                    tgt = inbound.get("target") or {}
                    if tid and "host" in tgt and "port" in tgt:
                        updated, err = osc_forwarder.update(tid, tgt)
                        if err is not None:
                            await ws.send(json.dumps({"type": "osc_error",
                                                       "action": "update",
                                                       "id": tid,
                                                       "error": err}))
                        elif updated is not None:
                            await broadcast({"type": "osc_state",
                                              "targets": osc_forwarder.snapshot()})
                elif action == "osc_remove":
                    tid = str(inbound.get("id", "")).strip()
                    if tid and osc_forwarder.remove(tid):
                        await broadcast({"type": "osc_state",
                                          "targets": osc_forwarder.snapshot()})
                elif action == "osc_auto_populate":
                    tid = str(inbound.get("id", "")).strip()
                    if tid:
                        try:
                            catalog = load_channel_catalog(CHANNEL_CATALOG_PATH)
                        except (OSError, json.JSONDecodeError) as exc:
                            await ws.send(json.dumps({"type": "osc_error",
                                                       "action": "auto_populate",
                                                       "id": tid,
                                                       "error": f"channel_catalog: {exc}"}))
                            continue
                        rows = schema_to_default_mappings(
                            modules_by_uid, module_types_by_uid, catalog)
                        if osc_forwarder.auto_populate(tid, rows) is not None:
                            await broadcast({"type": "osc_state",
                                              "targets": osc_forwarder.snapshot()})
            except (json.JSONDecodeError, ValueError, TypeError) as e:
                print(f"[bridge] bad WS message: {e}")
    finally:
        clients.discard(ws)


def _resolve_target(inbound: dict) -> str | None:
    """Resolve an inbound WS command to a UID token the hub accepts.

    Prefers explicit `uid`; falls back to `slot` via uid_by_slot for one
    deprecation cycle while frontend migrates. Returns None if neither
    resolves — caller logs and skips the command.
    """
    uid = inbound.get("uid")
    if uid:
        return str(uid)
    slot_val = inbound.get("slot")
    if slot_val is None:
        return None
    try:
        slot_int = int(slot_val)
    except (ValueError, TypeError):
        return None
    return uid_by_slot.get(slot_int)


async def _emit_transport_status(transport: Transport | None, *, connected: bool):
    """Cache + broadcast the current transport state."""
    msg = {
        "type": "transport_status",
        "transport": transport.name if transport else None,
        "address":   transport.address if transport else None,
        "label":     transport.label if transport else None,
        "connected": connected,
    }
    last_transport_status.update(msg)
    await broadcast(msg)


async def _run_ble_scan(duration: float):
    """Scan for HEX-* peripherals and broadcast each result + a 'done'
    sentinel so the UI can stop the spinner."""
    await broadcast({"type": "ble_scan_started", "duration": duration})
    try:
        results = await ble_scan_devices(duration=duration)
    except Exception as e:
        print(f"[bridge] BLE scan failed: {e!r}")
        await broadcast({"type": "ble_scan_error", "error": str(e)})
        return
    for r in results:
        await broadcast({"type": "ble_scan_result", **r})
    await broadcast({"type": "ble_scan_done", "count": len(results)})


async def _drive_transport(transport: Transport):
    """One read/write loop bound to a single open transport. Returns
    when the link drops or a switch is requested."""
    global current_transport
    exit_reason = "loop_ended"
    current_transport = transport
    await _emit_transport_status(transport, connected=True)
    _drop_pending_query_writes("fresh transport sync")
    # Layer 1 of rediscovery: first ask for authoritative topology, then
    # replay descriptors/status. Putting TOPO first keeps the small $T
    # snapshot ahead of larger descriptor bursts on BLE notify links.
    for cmd in ("TOPO", "STATUS", "ECA"):
        await _queue_query_command(cmd)
    await serial_write_queue.put("$L,INFO\n")
    recorder.note(f"transport connected: {transport.name} "
                  f"{transport.label} ({transport.address}); "
                  "queued $Q,TOPO + $Q,STATUS + $Q,ECA + $L,INFO")
    print(f"[bridge] {transport.name} connected: {transport.label} "
          f"({transport.address}) — queued $Q,TOPO + $Q,STATUS + $Q,ECA + $L,INFO")
    try:
        while transport.is_open:
            # Drain write queue
            while not serial_write_queue.empty():
                cmd = serial_write_queue.get_nowait()
                recorder.tx(cmd)
                try:
                    await transport.write(cmd.encode())
                    if transport.name == "ble":
                        await asyncio.sleep(0.08)
                except Exception as e:
                    exit_reason = f"write_failed: {e!r}"
                    recorder.note(exit_reason)
                    return
            # Switch requested?
            if not transport_request.empty():
                exit_reason = "switch_requested"
                return
            raw = await transport.read_line()
            if raw is None:
                err = getattr(transport, "last_error", None)
                exit_reason = "read_eof_or_disconnect"
                if err:
                    exit_reason += f": {err}"
                return  # EOF / disconnect
            if not raw:
                continue  # timeout — loop and re-check write queue
            recorder.rx(raw)
            if not raw.startswith("$"):
                line = raw.rstrip()
                if line:
                    marker = _classify_debug_line(line)
                    if marker:
                        recorder.note(f"{marker}: {line}")
                    print(f"[debug] {line}")
                    await broadcast({"type": "log", "line": line,
                                      "ts": int(time.time() * 1000)})
                continue
            try:
                msg = parse_line(raw)
            except Exception as e:
                print(f"[bridge] parse failed: {e!r} on {raw!r}")
                continue
            if msg:
                try:
                    await broadcast(msg)
                except Exception as e:
                    print(f"[bridge] broadcast failed: {e!r} "
                          f"type={msg.get('type')}")
    finally:
        recorder.note(f"transport disconnected: {transport.name} "
                      f"{transport.label} ({transport.address}); "
                      f"reason={exit_reason}")
        current_transport = None
        _clear_pending_query_state(f"transport disconnected: {exit_reason}")
        try:
            await transport.close()
        except Exception:
            pass
        clear_hub_runtime_state()
        await _emit_transport_status(None, connected=False)


async def transport_supervisor(initial_port: str | None = None):
    """Drives whichever transport is currently selected. Mutual-exclusion
    is intrinsic: there is at most one active `_drive_transport()` at a
    time. Switching is requested via `transport_request.put(spec)`:

        spec = ("serial", port_path)        # use SerialTransport
        spec = ("ble",    address, label)   # use BleTransport
        spec = ("none",)                    # disconnect, idle
    """
    pending = None
    if initial_port:
        pending = ("serial", initial_port)
    else:
        # If a paired BLE device is marked auto_reconnect, try it first.
        for d in _load_paired():
            if d.get("auto_reconnect"):
                pending = ("ble", d["address"], d.get("name") or d["address"])
                break

    while True:
        if pending is None:
            # Idle — wait for a request.
            await _emit_transport_status(None, connected=False)
            spec = await transport_request.get()
        else:
            spec = pending
            pending = None

        kind = spec[0]
        if kind == "none":
            recorder.note("transport request: none")
            continue

        # Build transport
        if kind == "serial":
            port = spec[1]
            transport: Transport = SerialTransport(port, BAUD)
        elif kind == "ble":
            addr = spec[1]
            label = spec[2] if len(spec) > 2 else addr
            transport = BleTransport(addr, label=label)
        else:
            print(f"[bridge] unknown transport spec: {spec!r}")
            recorder.note(f"unknown transport spec: {spec!r}")
            continue

        # Open with retry/wait semantics appropriate to each kind
        recorder.note(f"transport opening: {kind} {transport.label} "
                      f"({transport.address})")
        opened = await transport.open()
        if not opened:
            if kind == "serial":
                # Mirror old behaviour: wait for the port to reappear, but
                # bail out if a different transport is requested first.
                print(f"[bridge] {port} not present, polling…")
                recorder.note(f"serial open failed: {port}; polling")
                loop = asyncio.get_event_loop()
                while not opened:
                    if not transport_request.empty():
                        recorder.note(f"serial polling aborted by switch: {port}")
                        break
                    ser = await loop.run_in_executor(
                        None, lambda: serial_io.open_serial(port, BAUD, timeout=0.1))
                    if ser is not None:
                        try:
                            ser.close()
                        except Exception:
                            pass
                        recorder.note(f"serial port reappeared: {port}")
                        opened = await transport.open()
                        break
                    await asyncio.sleep(0.5)
                if not opened:
                    recorder.note(f"serial open abandoned: {port}")
                    continue
            else:
                print(f"[bridge] BLE open failed; staying idle")
                recorder.note(f"BLE open failed: {transport.label} "
                              f"({transport.address}); "
                              f"last_error={getattr(transport, 'last_error', None)}")
                await _emit_transport_status(None, connected=False)
                continue

        # Drive until disconnect or switch
        await _drive_transport(transport)

        # If the loop exited because of a switch request, pop it.
        if not transport_request.empty():
            try:
                pending = transport_request.get_nowait()
            except asyncio.QueueEmpty:
                pending = None
        elif kind == "serial":
            # Serial dropped on its own — auto-reconnect to same port.
            pending = ("serial", spec[1])
            recorder.note(f"serial auto-reconnect scheduled: {spec[1]}")
        elif kind == "ble":
            # BLE dropped — go idle (user must reconnect from UI).
            pending = None
            recorder.note("BLE disconnected; staying idle")


async def serial_loop(port: str):
    """Back-compat entry point used by main()."""
    await transport_supervisor(initial_port=port)


# Legacy single-transport implementation kept here as reference for the
# behavioural contract (write-queue draining, $Q,STATUS resync). Live code
# now goes through transport_supervisor → _drive_transport.
async def _serial_loop_legacy(port: str):
    loop = asyncio.get_event_loop()
    while True:
        ser = serial_io.open_serial(port, BAUD, timeout=0.1)
        if ser is None:
            print(f"[bridge] {port} not present, polling…")
            ser = await loop.run_in_executor(
                None, lambda: serial_io.wait_for_port(
                    port, BAUD, max_wait=float("inf")))
            if ser is None:
                continue
        try:
            print(f"[bridge] serial connected: {port}")
            # Layer 1 of rediscovery: hub may already have modules registered
            # from before we connected. Ask it to re-emit $H/$D for everything
            # in its registry so our msg_cache is populated for any browser
            # that connects later. Replays don't trigger re-discovery on the
            # CAN bus — they only dump what hub already knows.
            _drop_pending_query_writes("fresh serial sync")
            for cmd in ("TOPO", "STATUS", "ECA"):
                await _queue_query_command(cmd)
            await serial_write_queue.put("$L,INFO\n")
            print("[bridge] sent $Q,TOPO + $Q,STATUS + $Q,ECA + $L,INFO to hub (initial sync)")
            while True:
                # Drain write queue → send commands to hub
                while not serial_write_queue.empty():
                    cmd = serial_write_queue.get_nowait()
                    recorder.tx(cmd)
                    await loop.run_in_executor(
                        None, lambda c=cmd: ser.write(c.encode()))
                # Run blocking readline in executor so event loop stays free
                raw = await loop.run_in_executor(
                    None, lambda: ser.readline().decode("utf-8", errors="replace"))
                if not raw:
                    continue
                recorder.rx(raw)
                if not raw.startswith("$"):
                    line = raw.rstrip()
                    if line:
                        print(f"[debug] {line}")
                        await broadcast({"type": "log",
                                          "line": line,
                                          "ts": int(time.time() * 1000)})
                    continue
                try:
                    msg = parse_line(raw)
                except Exception as e:
                    # Defensive: a malformed hub line should never bring
                    # the serial loop down. Real serial drops still raise
                    # SerialException and trigger reconnect below.
                    print(f"[bridge] parse failed: {e!r} on {raw!r}")
                    continue
                if msg:
                    try:
                        await broadcast(msg)
                    except serial.SerialException:
                        raise
                    except Exception as e:
                        print(f"[bridge] broadcast failed: {e!r} "
                              f"type={msg.get('type')}")
        except serial.SerialException as e:
            print(f"[bridge] serial dropped: {e} — reconnecting…")
            try:
                ser.close()
            except Exception:
                pass


# ── Simple mock (backward-compatible) ────────────────────────────

async def mock_loop():
    print("[bridge] mock mode -- generating fake IMU data at 50 Hz")
    slot, mod_id = 1, "imuv2"
    modules[slot] = mod_id
    await broadcast({"type": "hello", "id": mod_id, "face": 1, "slot": slot,
                      "color": color_for(mod_id)})
    await broadcast({"type": "descriptor", "slot": slot,
                      "data": {"id": mod_id, "type": "imu", "rate": 50}})
    t0 = time.time()
    while True:
        t = time.time() - t0
        await broadcast({
            "type": "sensor", "slot": slot, "sensor": "imu",
            "ts": int(time.time() * 1000),
            "data": {"ax": round(math.sin(t * 2) * 0.1, 4),
                     "ay": round(math.cos(t * 2) * 0.1, 4),
                     "az": round(1.0 + math.sin(t) * 0.02, 4),
                     "gx": round(math.sin(t * 3) * 5, 2),
                     "gy": round(math.cos(t * 3) * 5, 2),
                     "gz": round(math.sin(t) * 2, 2)}})
        await asyncio.sleep(0.02)


# ── Interactive multi-module simulator ───────────────────────────

# Standard module face layout: 1P + 3R (P opposite + the two R adjacent to
# that opposite cluster on the half facing away from P). Faces 2 and 6 are
# physically closed (no connector). Hub has all 6 faces as R.
MODULE_FACE_KINDS = {1: "P", 3: "R", 4: "R", 5: "R"}
HUB_FACE_KINDS    = {1: "R", 2: "R", 3: "R", 4: "R", 5: "R", 6: "R"}

# Full descriptors matching WearBlocksDescriptor::serialize() output
SIM_MODULE_DEFS = {
    "imu": {
        "id": "imuv2", "slot": 1, "face": 1, "color": "#7CA1BB",
        "descriptor": {
            "id": "imuv2", "name": "6-Axis IMU", "cat": "motion_sensing",
            "color": "#7CA1BB", "ver": "2.0",
            "caps": [
                {"t": "sensor", "m": "acceleration", "ax": 3,
                 "rn": -16, "rx": 16, "res": 0.001, "dt": "float32[3]", "sr": [50]},
                {"t": "sensor", "m": "angular_velocity", "ax": 3,
                 "rn": -2000, "rx": 2000, "res": 0.1, "dt": "float32[3]", "sr": [50]},
            ],
            "affs": ["detect_gesture", "track_orientation", "count_repetitions"],
            "pwr": {"v": 3.3, "i": 3.5, "ip": 10},
            "phy": {"w": 4.2, "dim": [15, 15, 5], "plc": ["wrist", "forearm"]},
        },
        "hz": 50,
    },
    "hr": {
        "id": "hrv1", "slot": 2, "face": 2, "color": "#7B68EE",
        "descriptor": {
            "id": "hrv1", "name": "Heart Rate", "cat": "biometric",
            "color": "#7B68EE", "ver": "1.0",
            "caps": [
                {"t": "sensor", "m": "heart_rate", "ax": 1,
                 "rn": 30, "rx": 220, "res": 1, "dt": "float32", "sr": [10]},
                {"t": "sensor", "m": "spo2", "ax": 1,
                 "rn": 70, "rx": 100, "res": 0.1, "dt": "float32", "sr": [10]},
            ],
            "affs": ["monitor_heart", "detect_stress"],
            "pwr": {"v": 3.3, "i": 5.0, "ip": 20},
            "phy": {"w": 3.0, "dim": [15, 15, 5], "plc": ["wrist", "finger"]},
        },
        "hz": 10,
    },
    "temp": {
        "id": "tmpv1", "slot": 3, "face": 3, "color": "#F5A623",
        "descriptor": {
            "id": "tmpv1", "name": "Temp/Humidity", "cat": "environmental",
            "color": "#F5A623", "ver": "1.0",
            "caps": [
                {"t": "sensor", "m": "temperature", "ax": 1,
                 "rn": -40, "rx": 85, "res": 0.01, "dt": "float32", "sr": [1]},
                {"t": "sensor", "m": "humidity", "ax": 1,
                 "rn": 0, "rx": 100, "res": 0.1, "dt": "float32", "sr": [1]},
            ],
            "affs": ["measure_temperature", "measure_humidity"],
            "pwr": {"v": 3.3, "i": 1.0, "ip": 3},
            "phy": {"w": 2.5, "dim": [15, 15, 4], "plc": ["chest", "wrist"]},
        },
        "hz": 1,
    },
    "led": {
        "id": "ledv1", "slot": 5, "face": 5, "color": "#C68E9E",
        "descriptor": {
            "id": "ledv1", "name": "RGB LED Ring", "cat": "visual_output",
            "color": "#C68E9E", "ver": "1.0",
            "caps": [
                {"t": "actuator", "m": "rgb_light", "ax": 3,
                 "rn": 0, "rx": 255, "res": 1, "dt": "uint8[3]", "sr": []},
            ],
            "affs": ["visual_feedback", "status_indicator", "notification"],
            "pwr": {"v": 3.3, "i": 20, "ip": 400},
            "phy": {"w": 3.8, "dim": [20, 20, 4], "plc": ["wrist", "chest"]},
        },
        "hz": 0,  # actuator, no streaming
    },
    "vib": {
        "id": "vibv1", "slot": 4, "face": 4, "color": "#50C878",
        "descriptor": {
            "id": "vibv1", "name": "Vibration Motor", "cat": "haptic_output",
            "color": "#50C878", "ver": "1.0",
            "caps": [
                {"t": "actuator", "m": "vibration", "ax": 1,
                 "rn": 0, "rx": 255, "res": 1, "dt": "uint8", "sr": []},
            ],
            "affs": ["haptic_feedback", "notification", "guidance"],
            "pwr": {"v": 3.3, "i": 50, "ip": 150},
            "phy": {"w": 5.0, "dim": [15, 15, 6], "plc": ["wrist", "ankle"]},
        },
        "hz": 0,  # actuator, no streaming
    },
    "light": {
        "id": "lightv3", "slot": 6, "face": 6, "color": "#C1B496",
        "descriptor": {
            "id": "lightv3", "name": "Light Sensor", "cat": "light_sensing",
            "color": "#C1B496", "ver": "3.0",
            "caps": [
                {"t": "sensor", "m": "light", "ax": 1,
                 "rn": 0, "rx": 1, "res": 0.001, "dt": "float32", "sr": [25]},
            ],
            "affs": ["detect_ambient_light", "detect_cover"],
            "pwr": {"v": 3.3, "i": 1.0, "ip": 1.0},
            "phy": {"w": 2.0, "dim": [15, 15, 4], "plc": ["wrist", "chest"]},
        },
        "hz": 25,
    },
    "audio": {
        "id": "audiov1", "slot": 7, "face": 2, "color": "#9885BF",
        "descriptor": {
            "id": "audiov1", "name": "Audio Synth", "cat": "audio_output",
            "color": "#9885BF", "ver": "1.0",
            "caps": [
                {"t": "actuator", "m": "audio_synth", "ax": 2,
                 "rn": 0, "rx": 5000, "res": 1, "dt": "uint16[2]", "sr": []},
            ],
            "affs": ["audio_feedback", "tone_generation", "notification"],
            "pwr": {"v": 3.3, "i": 100, "ip": 500},
            "phy": {"w": 4.5, "dim": [20, 20, 5], "plc": ["wrist", "chest"]},
        },
        "hz": 0,  # actuator, no streaming
    },
    "loralog": {
        "id": "loralogv1", "slot": 10, "face": 4, "color": "#4FA7A1",
        "descriptor": {
            "id": "loralogv1", "name": "LoRa Logger",
            "cat": "wireless_uplink", "color": "#4FA7A1", "ver": "1.0",
            "caps": [
                {"t": "transport", "m": "lora_uplink", "ax": 1,
                 "rn": 0, "rx": 1, "res": 1, "dt": "batch", "sr": []},
                {"t": "logger", "m": "batch_log", "ax": 1,
                 "rn": 0, "rx": LOGGER_MAX_SUBSCRIPTIONS, "res": 1,
                 "dt": "record_batch", "sr": []},
            ],
            "affs": ["log_sensor_topics", "uplink_batches", "cache_offline"],
            "pwr": {"v": 3.3, "i": 38, "ip": 140},
            "phy": {"w": 8.0, "dim": [28, 28, 8], "plc": ["belt", "backpack"]},
            "cfg": [
                {"k": "logger_profile", "t": "bytes", "d": "empty",
                 "l": "Forward topics"},
            ],
        },
        "hz": 0,
    },
    "motor": {
        # Slots 8-10 belong to the two remote modules and LoRa logger in the
        # combined simulator. Slot 11 is the remaining ECA-addressable slot.
        "id": "motorv1", "slot": 11, "face": 1, "color": "#D97757",
        "descriptor": {
            "id": "motorv1", "name": "Dual DC Motor", "cat": "motor_output",
            "color": "#D97757", "ver": "1.0",
            "caps": [
                {"t": "actuator", "m": "dual_motor", "ax": 2,
                 "rn": -255, "rx": 255, "res": 1, "dt": "int16[2]", "sr": []},
            ],
            "affs": ["independent_motor_control"],
            "pwr": {"v": 5.0, "i": 100, "ip": 1000},
            "phy": {"w": 8.0, "dim": [32, 32, 8], "plc": ["robot"]},
        },
        "hz": 0,
    },
    "motor_hub": {
        "id": "motor_builtin", "slot": 0, "face": 0, "color": "#D97757",
        "builtin": True,
        "descriptor": {
            "id": "motor_builtin", "name": "Built-in Dual Motor",
            "cat": "motor_output", "color": "#D97757", "ver": "1.0",
            "caps": [
                {"t": "actuator", "m": "dual_motor", "ax": 2,
                 "rn": -255, "rx": 255, "res": 1, "dt": "int16[2]", "sr": []},
            ],
            "affs": ["independent_motor_control", "built_in"],
            "pwr": {"v": 5.0, "i": 100, "ip": 1000},
            "phy": {"w": 0.0, "dim": [0, 0, 0], "plc": ["internal"]},
        },
        "hz": 0,
    },
}

SIM_MODULE_DEFS["remote_temp"] = copy.deepcopy(SIM_MODULE_DEFS["temp"])
SIM_MODULE_DEFS["remote_temp"].update({
    "id": "tmpw1", "slot": 8, "face": 0, "remote": True,
    "data_type": "temp",
})
SIM_MODULE_DEFS["remote_temp"]["descriptor"].update({
    "id": "tmpw1", "name": "Remote Temp/Humidity",
})

SIM_MODULE_DEFS["remote_hr"] = copy.deepcopy(SIM_MODULE_DEFS["hr"])
SIM_MODULE_DEFS["remote_hr"].update({
    "id": "hrw1", "slot": 9, "face": 0, "remote": True,
    "data_type": "hr",
})
SIM_MODULE_DEFS["remote_hr"]["descriptor"].update({
    "id": "hrw1", "name": "Remote Heart Rate",
})


def _noise(scale: float = 0.01) -> float:
    return random.gauss(0, scale)


def sim_sensor_data(mod_type: str, t: float) -> dict | None:
    """Generate realistic sensor data for a given module type."""
    if mod_type == "imu":
        return {
            "ax": round(math.sin(t * 2.1) * 0.15 + _noise(0.02), 4),
            "ay": round(math.cos(t * 1.7) * 0.12 + _noise(0.02), 4),
            "az": round(1.0 + math.sin(t * 0.5) * 0.03 + _noise(0.01), 4),
            "gx": round(math.sin(t * 3.3) * 8.0 + _noise(0.5), 2),
            "gy": round(math.cos(t * 2.8) * 6.0 + _noise(0.5), 2),
            "gz": round(math.sin(t * 1.2) * 3.0 + _noise(0.3), 2),
        }
    if mod_type == "light":
        # Simulate ambient light: slow changes (day/night cycle) + small noise
        # Range 0..1 (normalized), mimics LDR voltage divider output
        base = 0.5 + math.sin(t * 0.05) * 0.3  # slow drift
        light = max(0.0, min(1.0, base + _noise(0.01)))
        return {"light": round(light, 3)}
    if mod_type == "hr":
        bpm = 72 + math.sin(t * 0.1) * 8 + _noise(2)
        spo2 = 97.5 + math.sin(t * 0.05) * 0.8 + _noise(0.2)
        return {
            "bpm": round(bpm, 1),
            "spo2": round(spo2, 1),
        }
    if mod_type == "temp":
        temp = 22.5 + math.sin(t * 0.02) * 1.5 + _noise(0.1)
        hum = 45.0 + math.sin(t * 0.03) * 5.0 + _noise(0.5)
        return {
            "celsius": round(temp, 2),
            "humidity": round(hum, 1),
        }
    return None


class SimModule:
    """A simulated module that streams data."""

    def __init__(self, mod_type: str):
        defn = SIM_MODULE_DEFS[mod_type]
        self.mod_type = mod_type
        self.data_type = defn.get("data_type", mod_type)
        self.remote = bool(defn.get("remote", False))
        self.mod_id = defn["id"]
        self.slot = defn["slot"]
        # Stable synthetic UID per slot — matches the 8-hex-char format the
        # real hub emits. Letting slot drive the uid keeps sim messages
        # deterministic across runs (the spike-injection CLI still addresses
        # by slot or module-type name; uid is for the wire only).
        # Chars must be valid hex (0-9, a-f) so the ECA bytecode encoder
        # can parse uid → u32. "FACE" is the prefix; slot fills the low 16 bits.
        self.uid = f"FACE{self.slot:04X}"
        self.face = 0 if self.remote else defn["face"]
        self.color = defn["color"]
        self.descriptor = defn["descriptor"]
        self.hz = defn["hz"]
        self.is_builtin = bool(defn.get("builtin", False))
        self.last_action_route: str | None = None
        self.last_action_cmd: int | None = None
        self.last_action_params: list[float] = []
        self.active = True
        self.t0 = time.time()
        # Register uid ↔ slot both ways so the bridge's inbound-WS routing
        # (host commands) and parse_line (future hub echoes) both resolve
        # correctly. Populate before first broadcast.
        uid_by_slot[self.slot] = self.uid
        slot_by_uid[self.uid] = self.slot
        modules_by_uid[self.uid] = self.mod_id
        # Actuator runtime state (only meaningful for LED/VIB modules; harmless
        # to carry on sensors). until_ms == 0 means "no expiry scheduled".
        self.led = {"r": 0, "g": 0, "b": 0, "brightness": 0,
                    "mode": "off", "until_ms": 0, "_deadline_ms": 0}
        self.vib = {"intensity": 0, "mode": "off", "until_ms": 0,
                    "_deadline_ms": 0}
        self.audio = {"frequency_hz": 0, "amplitude": 0, "mode": "off",
                      "until_ms": 0, "_deadline_ms": 0}
        self.motors = {
            1: {"mode": "stop", "speed": 0, "until_ms": 0,
                "_deadline_ms": 0},
            2: {"mode": "stop", "speed": 0, "until_ms": 0,
                "_deadline_ms": 0},
        }
        # One-shot sensor spike: {channel_id: (override_value, expires_ms)}.
        # Consumed by sim_sensor_data via _spike_override; auto-cleared.
        self.spikes: dict[int, tuple[float, int]] = {}

    async def send_hello(self):
        await broadcast({
            "type": "hello", "uid": self.uid,
            "id": self.mod_id, "face": self.face,
            "slot": self.slot, "color": self.color,
            "parent_uid": None, "parent_is_hub": not self.remote,
            "parent_remote": self.remote,
            "parent_face": self.face,
        })

    async def send_descriptor(self):
        # Inject face-kind layout (P/R per face) so the frontend can render
        # connector orientation badges. Stringify keys to match JSON behavior.
        desc = dict(self.descriptor)
        desc["face_kinds"] = {str(k): v for k, v in MODULE_FACE_KINDS.items()}
        await broadcast({"type": "descriptor", "uid": self.uid,
                          "slot": self.slot, "data": desc})

    async def send_sensor_tick(self):
        if self.hz <= 0 or not self.active:
            return
        t = time.time() - self.t0
        data = sim_sensor_data(self.data_type, t)
        if not data:
            return
        # Apply any one-shot spike overrides. A spike replaces the generator
        # output for a single channel until its expiry time passes.
        now_ms = _sim_monotonic_ms()
        ch_map = SIM_CHANNEL_MAP.get(self.data_type, {})
        if self.spikes:
            # Reverse lookup channel_id → data key so spikes can target CH.AX
            # directly regardless of the module's per-type remap.
            key_for = {v: k for k, v in ch_map.items()}
            expired = []
            for ch_id, (value, until) in self.spikes.items():
                if now_ms >= until:
                    expired.append(ch_id)
                    continue
                key = key_for.get(ch_id)
                if key is not None and key in data:
                    data[key] = value
            for ch_id in expired:
                self.spikes.pop(ch_id, None)
        # Feed the ECA engine so rule conditions can see the same values
        # the WS clients see. Map this module's per-type data keys to the
        # canonical channel ids.
        for key, ch_id in ch_map.items():
            if key in data:
                eca.update_sensor(self.slot, int(ch_id), float(data[key]))
        sensor_type = CAT_MAP.get(self.descriptor.get("cat", ""), self.data_type)
        # Emit one v2-shaped per-channel frame per channel in this module's
        # capability map — this is what the real hub emits on the wire. Keep
        # the legacy batched frame as a secondary broadcast during the
        # frontend migration window so the sensor panel keeps rendering
        # until commit 4 switches it over.
        for key, ch_id in ch_map.items():
            if key not in data:
                continue
            await broadcast({
                "type": "sensor", "uid": self.uid, "slot": self.slot,
                "sensor": sensor_type, "channel_id": int(ch_id),
                "value": float(data[key]), "ts": now_ms,
            })
            await _sim_logger_consume_sensor(self.uid, int(ch_id),
                                             float(data[key]), now_ms)
        await broadcast({
            "type": "sensor", "uid": self.uid, "slot": self.slot,
            "sensor": sensor_type, "ts": now_ms, "data": data,
            "legacy": True,
        })


# Active simulated modules
sim_modules: dict[int, SimModule] = {}  # slot → SimModule
# Parent tracking for stacked modules:  child_slot → (parent_slot, parent_face)
sim_parents: dict[int, tuple[int, int]] = {}
sim_transport_modes: dict[str, str] = {}
sim_logger_profiles: dict[str, dict] = {}
sim_logger_status: dict[str, dict] = {}
sim_eca_b64: str = ""
sim_eca_raw_len: int = 0
SIM_DEFAULT_TRANSPORT_MODE = "can_primary_wifi_fallback"
SIM_WIFI_SSID = "HEX-SIM-HUB"
SIM_WIFI_PASSWORD = "hex-sim-pass"
SIM_WIFI_TOKEN = "sim-osc-token"
SIM_WIFI_IP = "192.168.4.1"
SIM_WIFI_PORT = 9000

# Set by sim_loop() so the WS handler can inject sim commands (e.g.
# "demo1") from the browser preset buttons.
sim_cmd_queue: asyncio.Queue | None = None


def _slot_for_type(mod_type: str) -> int | None:
    defn = SIM_MODULE_DEFS.get(mod_type)
    return defn["slot"] if defn else None


def _resolve_slot(token: str) -> int | None:
    """Accept either a numeric slot or a module-type name."""
    token = token.strip().lower()
    if not token:
        return None
    if token.isdigit():
        return int(token)
    return _slot_for_type(token)


async def sim_stack(child_slot: int, parent_slot: int, parent_face: int):
    if child_slot not in sim_modules:
        print(f"  [sim] stack: child slot {child_slot} not connected")
        return
    if parent_slot not in sim_modules:
        print(f"  [sim] stack: parent slot {parent_slot} not connected")
        return
    if child_slot == parent_slot:
        print(f"  [sim] stack: cannot stack module on itself")
        return
    # Remember the child's original hub face so we can restore it on unstack.
    child = sim_modules[child_slot]
    parent = sim_modules[parent_slot]
    orig_face = child.face
    sim_parents[child_slot] = (parent_slot, parent_face)
    # Mirror real hub behaviour: a stacked child does not occupy any hub face.
    # We broadcast face_swap(old → 0) first so the frontend removes the module
    # from the hub face bar, *then* broadcast child_stack to link it visually
    # as a child of the parent.
    if orig_face != 0:
        child._orig_hub_face = orig_face  # stash for unstack
        child.face = 0
        await broadcast({"type": "face_swap", "uid": child.uid,
                         "slot": child_slot,
                         "old_parent_uid": None, "old_parent_is_hub": True,
                         "old_face": orig_face,
                         "new_parent_uid": parent.uid,
                         "new_parent_is_hub": False,
                         "new_face": 0})
        # Late-joining WS clients replay the cached hello — update it so
        # they don't see the child re-appearing on its old hub face.
        cached = (msg_cache_by_uid.get(child.uid, {}).get("hello")
                  or msg_cache.get(child_slot, {}).get("hello"))
        if cached:
            cached["face"] = 0
            cached["parent_face"] = 0
    await broadcast({"type": "child_stack",
                     "parent_uid": parent.uid, "child_uid": child.uid,
                     "pending": False,
                     "parent_slot": parent_slot, "child_slot": child_slot,
                     "parent_face": parent_face})
    c = child.mod_type
    p = parent.mod_type
    print(f"  [sim] ⬆ stacked {c} (slot {child_slot}) onto "
          f"{p} (slot {parent_slot}) face {parent_face}")


async def sim_unstack(child_slot: int):
    if child_slot not in sim_parents:
        print(f"  [sim] unstack: slot {child_slot} is not stacked")
        return
    parent_slot, parent_face = sim_parents.pop(child_slot)
    child = sim_modules.get(child_slot)
    parent = sim_modules.get(parent_slot)
    child_uid = child.uid if child else None
    parent_uid = parent.uid if parent else None
    await broadcast({"type": "child_unstack",
                     "parent_uid": parent_uid, "child_uid": child_uid,
                     "pending": False,
                     "parent_slot": parent_slot, "child_slot": child_slot,
                     "parent_face": parent_face})
    # Restore child's original hub face (if we stashed one on stack).
    if child is not None:
        restored = getattr(child, "_orig_hub_face", None)
        if restored and child.face == 0:
            child.face = restored
            await broadcast({"type": "face_swap", "uid": child.uid,
                             "slot": child_slot,
                             "old_parent_uid": parent_uid,
                             "old_parent_is_hub": False, "old_face": 0,
                             "new_parent_uid": None,
                             "new_parent_is_hub": True,
                             "new_face": restored})
            cached = (msg_cache_by_uid.get(child.uid, {}).get("hello")
                      or msg_cache.get(child_slot, {}).get("hello"))
            if cached:
                cached["face"] = restored
                cached["parent_face"] = restored
    print(f"  [sim] ⬇ unstacked slot {child_slot} from "
          f"slot {parent_slot} face {parent_face}")


# ── ECA action dispatch + sim command consumer ──────────────────

def _u16_be(b0: int, b1: int) -> int:
    """Decode a big-endian u16 from two bytes — matches eca-encoder.js u16()."""
    return ((b0 & 0xFF) << 8) | (b1 & 0xFF)


def dispatch_action(act: EcaAction) -> None:
    """ECA on_action callback — apply an actuator action to SimModule state.

    Param semantics (v3): the engine has already resolved each typed-ref
    param to a float in `act.vals`. The action's `target` is a module UID;
    we translate it via slot_by_uid to find the sim's slot.
    See WearBlocksECA.h:WBActCmd for the per-cmd param schema.
    """
    # Translate uid → sim slot. UIDs are stored as 8-hex-char strings in
    # slot_by_uid, while the engine carries them as a u32 — same value.
    uid_hex = f"{act.target:08X}"
    target_slot = slot_by_uid.get(uid_hex)
    if target_slot is None:
        print(f"  [sim] ECA action for unknown uid={uid_hex} — ignored")
        return
    mod = sim_modules.get(target_slot)
    if mod is None:
        print(f"  [sim] ECA action for empty slot {target_slot} — ignored")
        return
    mod.last_action_route = "local" if mod.is_builtin else "can"
    cmd = act.cmd
    mod.last_action_cmd = int(cmd)
    mod.last_action_params = [float(value) for value in (act.vals or [])]
    now_ms = _sim_monotonic_ms()
    wall_ms = int(time.time() * 1000)
    vals = act.vals or []

    def vget(i: int, default: float = 0.0) -> float:
        return vals[i] if i < len(vals) else default

    def vbyte(i: int) -> int:
        return max(0, min(255, int(vget(i) + 0.5)))

    def deadlines(duration_ms: int) -> dict:
        if act.mode == ActionMode.STREAM:
            duration_ms = max(100, min(2550, act.update_interval_ms * 3))
        duration_ms = max(0, duration_ms)
        return {
            "until_ms": wall_ms + duration_ms if duration_ms > 0 else 0,
            "_deadline_ms": now_ms + duration_ms if duration_ms > 0 else 0,
        }

    # ── LED commands ───────────────────────────────
    if cmd in (Act.LED_OFF, Act.LED_STOP):
        mod.led = {"r": 0, "g": 0, "b": 0, "brightness": 0,
                   "mode": "off", "until_ms": 0, "_deadline_ms": 0}
    elif cmd == Act.LED_SOLID:
        # 3 params: R, G, B. Lifecycle duration is carried separately in v4.
        mod.led = {"r": vbyte(0), "g": vbyte(1), "b": vbyte(2),
                   "brightness": 255, "mode": "solid",
                   **deadlines(act.duration_ms)}
    elif cmd in (Act.LED_BLINK, Act.LED_BREATHE, Act.LED_RAMP, Act.LED_RAINBOW):
        # Reserved — module_led v3 doesn't implement these. Treat as SOLID
        # with the first 3 params (forward-compatible passthrough).
        mod.led = {"r": vbyte(0), "g": vbyte(1), "b": vbyte(2),
                   "brightness": 255, "mode": "solid",
                   **deadlines(act.duration_ms)}

    # ── Vibration commands ─────────────────────────
    elif cmd == Act.VIBRATE:
        intensity = vbyte(0)
        dur_ms = act.duration_ms or max(0, int(vget(1) + 0.5))
        mod.vib = {"intensity": intensity, "mode": "on",
                   **deadlines(dur_ms)}
    elif cmd == Act.VIBRATE_PULSE:
        intensity = vbyte(0)
        on_ms = max(1, int(vget(1, 100) + 0.5))
        off_ms = max(0, int(vget(2, 100) + 0.5))
        count = vbyte(3) or 1
        total = act.duration_ms or ((on_ms + off_ms) * max(1, count))
        mod.vib = {"intensity": intensity, "mode": "pulse",
                   "on_ms": on_ms, "off_ms": off_ms, "count": count,
                   **deadlines(total)}
    elif cmd == Act.VIBRATE_RAMP:
        total = act.duration_ms
        mod.vib = {"intensity": vbyte(1), "from": vbyte(0), "mode": "ramp",
                   **deadlines(total)}
    elif cmd == Act.VIBRATE_STOP:
        mod.vib = {"intensity": 0, "mode": "off", "until_ms": 0,
                   "_deadline_ms": 0}

    # ── Audio commands ─────────────────────────────
    elif cmd == Act.AUDIO_SET_TONE:
        mod.audio = {"frequency_hz": max(0, min(65535, int(vget(0) + 0.5))),
                     "amplitude": vbyte(1), "mode": "tone",
                     **deadlines(act.duration_ms)}
    elif cmd == Act.AUDIO_STOP:
        mod.audio = {"frequency_hz": 0, "amplitude": 0, "mode": "off",
                     "until_ms": 0, "_deadline_ms": 0}

    # ── Dual DC motor command ───────────────────────
    elif cmd == Act.MOTOR_SET:
        motor = int(vget(0) + 0.5)
        mode = int(vget(1) + 0.5)
        speed = vbyte(2)
        duration_ms = max(0, min(65535, int(vget(3) + 0.5)))
        if motor not in (1, 2) or mode not in (0, 1, 2):
            print(f"  [sim] invalid MOTOR_SET motor={motor} mode={mode} — ignored")
            return
        if mode == 0 or speed == 0:
            mod.motors[motor] = {
                "mode": "stop", "speed": 0, "until_ms": 0,
                "_deadline_ms": 0,
            }
        else:
            mod.motors[motor] = {
                "mode": "forward" if mode == 1 else "reverse",
                "speed": speed,
                **deadlines(duration_ms),
            }

    print(f"  [sim] ECA fired: target_uid={uid_hex} (slot={target_slot}) cmd={cmd}")


# Bind the engine to the dispatcher now that dispatch_action exists.
eca._on_action = dispatch_action

# v4 ECA bytecode is uid-keyed; the engine asks back via this hook to
# translate uid (u32) → sim slot for sensor cache lookups inside SLOT refs.
# Same shape as the real hub's registry.findByUid().
def _sim_uid_to_slot(uid_u32: int) -> int:
    return slot_by_uid.get(f"{uid_u32:08X}", 0) or 0
eca.set_uid_resolver(_sim_uid_to_slot)


def expire_actuator_state(mod: SimModule, now_ms: int) -> None:
    """Expire timed actuator channels without coupling independent outputs."""
    led_deadline = mod.led.get("_deadline_ms", 0)
    if led_deadline and now_ms >= led_deadline:
        mod.led = {"r": 0, "g": 0, "b": 0, "brightness": 0,
                   "mode": "off", "until_ms": 0, "_deadline_ms": 0}
    vib_deadline = mod.vib.get("_deadline_ms", 0)
    if vib_deadline and now_ms >= vib_deadline:
        mod.vib = {"intensity": 0, "mode": "off", "until_ms": 0,
                   "_deadline_ms": 0}
    audio_deadline = mod.audio.get("_deadline_ms", 0)
    if audio_deadline and now_ms >= audio_deadline:
        mod.audio = {"frequency_hz": 0, "amplitude": 0, "mode": "off",
                     "until_ms": 0, "_deadline_ms": 0}
    for motor in (1, 2):
        deadline = mod.motors[motor].get("_deadline_ms", 0)
        if deadline and now_ms >= deadline:
            mod.motors[motor] = {
                "mode": "stop", "speed": 0, "until_ms": 0,
                "_deadline_ms": 0,
            }


def _resolve_sim_target(token: str) -> int | None:
    """Resolve a $A/$TE/$TD/$TA argument to a sim slot.

    Accepts a UID (8-hex), a numeric slot, or a module-type name — the sim
    command surface is historically lenient and the real hub's UID format
    is already handled via slot_by_uid.
    """
    token = token.strip()
    if not token:
        return None
    if token in slot_by_uid:
        slot = slot_by_uid[token]
        return slot if slot in sim_modules else None
    if token.isdigit():
        slot = int(token)
        return slot if slot in sim_modules else None
    return _slot_for_type(token.lower())


def _sim_action_from_wire(target_uid: int, command: int,
                          raw: list[int]) -> EcaAction:
    """Decode the Hub's v4 actuator payload bytes into simulator semantics."""
    values: list[float] = []
    duration_ms = 0
    if command in (Act.LED_SOLID, Act.LED_RAMP, Act.LED_BREATHE,
                   Act.LED_BLINK, Act.LED_RAINBOW):
        values = [float(value) for value in raw[:3]]
        duration_ms = _wire_u32_be(raw, 3)
    elif command == Act.VIBRATE:
        values = [float(raw[0] if raw else 0)]
        duration_ms = _wire_u32_be(raw, 1)
    elif command == Act.VIBRATE_PULSE:
        values = [
            float(raw[0] if len(raw) > 0 else 0),
            float((raw[1] if len(raw) > 1 else 10) * 10),
            float((raw[2] if len(raw) > 2 else 10) * 10),
            float(raw[3] if len(raw) > 3 else 1),
        ]
    elif command == Act.VIBRATE_RAMP:
        values = [float(raw[0] if raw else 0),
                  float(raw[1] if len(raw) > 1 else 0)]
        duration_ms = _wire_u32_be(raw, 2)
    elif command == Act.AUDIO_SET_TONE:
        frequency = (raw[0] if raw else 0) \
            | ((raw[1] if len(raw) > 1 else 0) << 8)
        values = [float(frequency), float(raw[2] if len(raw) > 2 else 0)]
        duration_ms = _wire_u32_be(raw, 3)
    elif command == Act.MOTOR_SET:
        values = [
            float(raw[0] if len(raw) > 0 else 0),
            float(raw[1] if len(raw) > 1 else 0),
            float(raw[2] if len(raw) > 2 else 0),
            float(((raw[3] << 8) | raw[4]) if len(raw) > 4 else 0),
        ]

    from wb_eca import ActionParam, REF as _REF
    params_typed = [ActionParam(type=_REF.CONST, id=0, ch=0, value=value)
                    for value in values]
    return EcaAction(target=target_uid, cmd=command,
                     duration_ms=duration_ms,
                     params=params_typed, vals=values)


def _sim_actuator_message(mod: SimModule, slot: int, command: int,
                          raw: list[int], request_id: str = "") -> dict:
    return {
        "type": "actuator_state",
        "uid": mod.uid,
        "slot": slot,
        "cmd": command,
        "params": list(raw),
        "request_id": request_id or None,
        "source": "simulator",
        "confirmed": True,
        "led": {k: v for k, v in mod.led.items() if not k.startswith("_")},
        "vib": {k: v for k, v in mod.vib.items() if not k.startswith("_")},
        "audio": {k: v for k, v in mod.audio.items() if not k.startswith("_")},
        "motors": {
            str(index): {k: v for k, v in state.items()
                         if not k.startswith("_")}
            for index, state in mod.motors.items()
        },
    }


def _parse_sim_command(line: str) -> None:
    """Route a $-prefixed serial line synchronously into the ECA engine.
    Called from sim_command_consumer; safe to also call from anywhere that
    has already parsed a serial line. Returns None; emits log + ack via
    broadcast (scheduled as a task)."""
    line = line.strip()
    if not line.startswith("$"):
        return
    global sim_eca_b64, sim_eca_raw_len

    async def _ack(text: str, ok: bool = True):
        await broadcast({"type": "command_ack",
                         "status": "ok" if ok else "err",
                         "text": text,
                         "ts": int(time.time() * 1000)})

    try:
        if line.startswith("$P "):
            b64 = line[3:].strip()
            raw = base64.b64decode(b64)
            ok = eca.load_program(raw)
            text = (f"P loaded ({len(raw)} bytes, {eca.num_vcs()} VCs, "
                    f"{eca.num_rules()} rules)" if ok else "P load failed")
            asyncio.create_task(_ack(text, ok))
            print(f"  [sim] {text}")
            if ok:
                sim_eca_b64 = b64
                sim_eca_raw_len = len(raw)
                # Match real hub: $P also auto-runs.
                eca.run_program()
                asyncio.create_task(_ack("running"))
        elif line == "$PR":
            eca.run_program()
            asyncio.create_task(_ack("running"))
            print("  [sim] ECA running")
        elif line == "$PS":
            eca.stop_program()
            asyncio.create_task(_ack("stopped"))
            print("  [sim] ECA stopped")
        elif line == "$PC":
            eca.clear_program()
            sim_eca_b64 = ""
            sim_eca_raw_len = 0
            # Reset all actuators when program cleared.
            for s, m in sim_modules.items():
                m.led = {"r": 0, "g": 0, "b": 0, "brightness": 0,
                         "mode": "off", "until_ms": 0, "_deadline_ms": 0}
                m.vib = {"intensity": 0, "mode": "off", "until_ms": 0,
                         "_deadline_ms": 0}
                m.audio = {"frequency_hz": 0, "amplitude": 0, "mode": "off",
                           "until_ms": 0, "_deadline_ms": 0}
                m.motors = {
                    1: {"mode": "stop", "speed": 0, "until_ms": 0,
                        "_deadline_ms": 0},
                    2: {"mode": "stop", "speed": 0, "until_ms": 0,
                        "_deadline_ms": 0},
                }
            asyncio.create_task(_ack("cleared"))
            print("  [sim] ECA cleared")
        elif line.startswith(("$AO ", "$A ")):
            # $A <uid|slot> <cmd> <p0..p9>   — v2 hub addresses by UID; we
            # still accept a numeric slot for legacy host commands until the
            # frontend migration lands.
            is_osc = line.startswith("$AO ")
            parts = line[4 if is_osc else 3:].split()
            request_id = parts.pop(0) if is_osc and parts else ""
            if len(parts) < 2:
                prefix = f"AO {request_id}" if is_osc else "$A"
                asyncio.create_task(_ack(f"{prefix}: need target + cmd", ok=False))
                return
            target = parts[0]
            slot = _resolve_sim_target(target)
            if slot is None:
                prefix = f"AO {request_id}" if is_osc else "$A"
                asyncio.create_task(_ack(f"{prefix} bad_target {target}", ok=False))
                return
            cmd = int(parts[1])
            mod = sim_modules.get(slot)
            target_uid = int(mod.uid, 16) if (mod and mod.uid) else 0
            raw = [max(0, min(255, int(p))) for p in parts[2:]][:10]
            dispatch_action(_sim_action_from_wire(target_uid, cmd, raw))
            if is_osc:
                asyncio.create_task(_ack(
                    f"AO {request_id} uid={mod.uid} slot={slot} cmd={cmd} route=sim"))
                asyncio.create_task(broadcast(
                    _sim_actuator_message(mod, slot, cmd, raw, request_id)))
            else:
                asyncio.create_task(_ack(f"A slot={slot} cmd={cmd}"))
        elif line.startswith(("$TE", "$TD", "$TA")):
            # $TE/$TD <uid|slot> <ch>   /   $TA <uid|slot>
            # Sim has no CAN to forward to; resolve-and-ack so the frontend
            # sees the ack shape it expects from the real hub.
            parts = line.split()
            op = parts[0][1:]  # "TE", "TD", "TA"
            target = parts[1] if len(parts) >= 2 else ""
            slot = _resolve_sim_target(target) if target else None
            if target and slot is None:
                asyncio.create_task(_ack(f"{op} bad_target {target}", ok=False))
            else:
                print(f"  [sim] (topic op ignored in sim) {line}")
                asyncio.create_task(_ack(f"{op} slot={slot}"))
        elif line == "$W,INFO":
            asyncio.create_task(_emit_sim_wireless_info())
        elif line.startswith("$W,CONFIG "):
            parts = line.split()
            if len(parts) < 3:
                asyncio.create_task(_ack("$W,CONFIG: need target + mode", ok=False))
                return
            target = parts[1].strip().upper()
            mode = parts[2].strip()
            if mode not in WIRELESS_TRANSPORT_MODES:
                asyncio.create_task(_ack(f"W bad_mode {mode}", ok=False))
                return
            if target == "ALL":
                mods = list(sim_modules.values())
            else:
                slot = _resolve_sim_target(target)
                if slot is None:
                    asyncio.create_task(_ack(f"W bad_target {target}", ok=False))
                    return
                mods = [sim_modules[slot]]
            for mod in mods:
                sim_transport_modes[mod.uid] = mode
                asyncio.create_task(_emit_sim_link_state(mod.uid))
            print(f"  [sim] wireless config {target} -> {mode}")
            asyncio.create_task(_ack(f"W CONFIG {target} {mode}"))
        elif line == "$L,INFO":
            asyncio.create_task(_emit_sim_logger_info())
        elif line.startswith("$L,CONFIG "):
            parts = line.split(maxsplit=2)
            if len(parts) < 3:
                asyncio.create_task(_ack("$L,CONFIG: need target + profile", ok=False))
                return
            target = parts[1].strip().upper()
            slot = _resolve_sim_target(target)
            if slot is None or slot not in sim_modules:
                asyncio.create_task(_ack(f"L bad_target {target}", ok=False))
                return
            mod = sim_modules[slot]
            if not _module_is_logger_uid(mod.uid):
                asyncio.create_task(_ack(f"L target_not_logger {target}", ok=False))
                return
            raw = base64.b64decode(parts[2].strip())
            decoded = decode_logger_profile(raw)
            sim_logger_profiles[mod.uid] = decoded
            stats = _sim_logger_status_for(mod.uid)
            stats["config_rev"] = decoded["config_rev"]
            stats["queue_depth"] = 0
            stats["last_emit"] = {}
            stats["last_value"] = {}
            asyncio.create_task(broadcast({
                "type": "logger_config",
                "uid": mod.uid,
                "slot": mod.slot,
                "config_rev": decoded["config_rev"],
                "subscriptions": decoded["subscriptions"],
            }))
            asyncio.create_task(_emit_sim_logger_status(mod.uid))
            print(f"  [sim] logger config {mod.uid} "
                  f"rev={decoded['config_rev']} subs={len(decoded['subscriptions'])}")
            asyncio.create_task(_ack(f"L CONFIG {mod.uid} rev={decoded['config_rev']}"))
        elif line.startswith("$Q,") or line == "$Q":
            # $Q,TOPO / $Q,STATUS / $Q,DISCOVER — sim has no real registry
            # to replay, but TOPO matters for frontend reconciliation
            # testing: emit one $T row per active module + a trailing
            # $Q,DONE so the frontend's reconcile path fires.
            cmd = line[3:].strip() if "," in line else ""
            if cmd == "ECA":
                asyncio.create_task(_emit_sim_eca_snapshot())
            elif cmd == "TOPO":
                asyncio.create_task(_emit_sim_topology())
            else:
                # STATUS/DISCOVER: modules already broadcast on +type, so
                # there's nothing to replay. Just terminate so the
                # frontend's pending query state resolves cleanly.
                asyncio.create_task(_emit_sim_query_done(cmd or "Q"))
        else:
            print(f"  [sim] unhandled serial line: {line}")
    except Exception as e:
        print(f"  [sim] error handling {line!r}: {e}")
        asyncio.create_task(_ack(f"error: {e}", ok=False))


async def _emit_sim_topology():
    """Mirror the real hub's $Q,TOPO reply: one topology message per
    sim_module, then query_done. Lets the frontend reconcile its
    _children + module.face from the sim's authoritative state."""
    for slot, mod in sorted(sim_modules.items()):
        if mod.remote:
            await broadcast({
                "type": "topology", "uid": mod.uid, "slot": slot,
                "parent_uid": None, "parent_is_hub": False,
                "parent_remote": True,
                "parent_face": 0,
            })
        elif slot in sim_parents:
            parent_slot, parent_face = sim_parents[slot]
            parent = sim_modules.get(parent_slot)
            parent_uid = parent.uid if parent else None
            await broadcast({
                "type": "topology", "uid": mod.uid, "slot": slot,
                "parent_uid": parent_uid, "parent_is_hub": False,
                "parent_remote": False,
                "parent_face": parent_face,
            })
        else:
            await broadcast({
                "type": "topology", "uid": mod.uid, "slot": slot,
                "parent_uid": None, "parent_is_hub": True,
                "parent_remote": False,
                "parent_face": mod.face,
            })
    _consume_tracked_query_done("TOPO")
    await broadcast({"type": "query_done", "command": "TOPO"})
    print(f"  [sim] $Q,TOPO replied: {len(sim_modules)} rows + DONE")


async def _emit_sim_query_done(cmd: str):
    command = str(cmd or "").upper()
    _consume_tracked_query_done(command)
    await broadcast({"type": "query_done", "command": command})
    print(f"  [sim] $Q,{cmd} → DONE (no replay)")


def _sim_active_link_for_mode(mode: str) -> str:
    if mode == "wifi_only" or mode == "wifi_primary_can_fallback":
        return "wifi"
    if mode == "dual_send_debug":
        return "dual"
    return "can"


async def _emit_sim_link_state(uid: str):
    slot = slot_by_uid.get(uid)
    mod = sim_modules.get(slot) if slot is not None else None
    if not mod:
        return
    mode = sim_transport_modes.get(uid, SIM_DEFAULT_TRANSPORT_MODE)
    active_link = _sim_active_link_for_mode(mode)
    if mod.remote and active_link == "can":
        active_link = "wifi"
    ip = f"192.168.4.{100 + mod.slot}" if active_link in ("wifi", "dual") else ""
    await broadcast({
        "type": "link_state",
        "uid": uid,
        "slot": mod.slot,
        "active_link": active_link,
        "transport_mode": mode,
        "topology_state": "remote_unplaced" if mod.remote else "physical",
        "ip": ip,
        "port": SIM_WIFI_PORT if ip else 0,
    })


def _sim_logger_status_for(uid: str) -> dict:
    stats = sim_logger_status.setdefault(uid, {
        "queue_depth": 0,
        "dropped_count": 0,
        "last_ack_ms": 0,
        "rssi": -91.0,
        "snr": 7.5,
        "time_quality": 1,
        "config_rev": 0,
        "last_emit": {},
        "last_value": {},
    })
    return stats


async def _emit_sim_logger_status(uid: str):
    slot = slot_by_uid.get(uid)
    stats = _sim_logger_status_for(uid)
    await broadcast({
        "type": "logger_status",
        "uid": uid,
        "slot": slot,
        "queue_depth": int(stats.get("queue_depth", 0)),
        "dropped_count": int(stats.get("dropped_count", 0)),
        "last_ack_ms": int(stats.get("last_ack_ms", 0)),
        "rssi": float(stats.get("rssi", -91.0)),
        "snr": float(stats.get("snr", 7.5)),
        "time_quality": int(stats.get("time_quality", 1)),
        "config_rev": int(stats.get("config_rev", 0)),
    })


async def _emit_sim_logger_info():
    count = 0
    for mod in sorted(sim_modules.values(), key=lambda m: m.slot):
        if _module_is_logger_uid(mod.uid):
            count += 1
            await _emit_sim_logger_status(mod.uid)
    print(f"  [sim] $L,INFO replied: {count} logger row(s)")


def _sim_logger_should_queue(logger_uid: str, sub: dict, value: float,
                             now_ms: int) -> bool:
    stats = _sim_logger_status_for(logger_uid)
    key = (sub["source_uid"], int(sub["channel_id"]), sub["record_type"])
    last_emit = stats.setdefault("last_emit", {})
    last_value = stats.setdefault("last_value", {})
    elapsed = now_ms - int(last_emit.get(key, 0))
    min_interval = int(sub.get("min_interval_ms", 0))
    mode = sub.get("mode", "latest_interval")
    if mode == "event_only":
        return True
    if mode == "on_change":
        if key not in last_value:
            return True
        threshold = float(sub.get("threshold", 0.0))
        if abs(value - float(last_value[key])) < threshold:
            return False
        return min_interval == 0 or elapsed >= min_interval
    return min_interval == 0 or elapsed >= min_interval
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
