zmk5566/Hexblocks/frontend/bridge/test_osc_bridge.py

"""Tests for osc_forwarder.py.

Run with:  python -m pytest frontend/bridge/test_osc_bridge.py -v

Spins up a real asyncio UDP listener on 127.0.0.1:<ephemeral_port> for each
case so we exercise the end-to-end pythonosc path instead of mocking
SimpleUDPClient. Slow-consumer cases are simulated by stalling the worker
queue, not by holding the UDP socket.
"""
from __future__ import annotations

import asyncio
import json
import socket
import struct
import time

import pytest

from pathlib import Path

from osc_forwarder import (
    OscForwarder,
    OscMapping,
    OscTarget,
    OscWorker,
    _coarse_match,
    _msg_to_source_keys,
    _pattern_matches,
    load_channel_catalog,
    schema_to_default_mappings,
)

REAL_CATALOG_PATH = Path(__file__).resolve().parent.parent / "channel_catalog.json"


# ── UDP listener helper ────────────────────────────────────────────

class OscRx(asyncio.DatagramProtocol):
    """Tiny OSC parser — single-message, float32 arg, no bundles."""

    def __init__(self):
        self.received: list[tuple[str, float]] = []

    def datagram_received(self, data: bytes, addr) -> None:
        self.received.append(self._parse(data))

    @staticmethod
    def _parse(data: bytes) -> tuple[str, float]:
        # OSC: address (null-padded to 4) + type tag (",f" padded) + 4-byte float
        idx = data.index(b"\x00")
        address = data[:idx].decode("ascii")
        # round up to next multiple of 4 after the null
        addr_end = (idx + 4) & ~3
        # type tag starts at addr_end, e.g. b",f\x00\x00"
        tag_end = addr_end + 4
        value = struct.unpack(">f", data[tag_end:tag_end + 4])[0]
        return address, float(value)


async def _listener_on_free_port():
    loop = asyncio.get_running_loop()
    rx = OscRx()
    transport, _ = await loop.create_datagram_endpoint(
        lambda: rx, local_addr=("127.0.0.1", 0))
    port = transport.get_extra_info("sockname")[1]
    return rx, transport, port


async def _drain(timeout=0.2):
    """Yield the loop a few times so queued sends actually leave the socket."""
    end = time.monotonic() + timeout
    while time.monotonic() < end:
        await asyncio.sleep(0.01)


# ── Pure-function tests (no socket) ────────────────────────────────

def test_pattern_matches_exact_and_wildcard():
    assert _pattern_matches("sensor/FACE0003/0", "sensor/FACE0003/0")
    assert _pattern_matches("sensor/*/0", "sensor/FACE0003/0")
    assert _pattern_matches("sensor/FACE0003/*", "sensor/FACE0003/9")
    assert _pattern_matches("sensor/*/*", "sensor/FACE0003/9")
    assert not _pattern_matches("sensor/FACE0003/0", "sensor/FACE0003/1")
    assert not _pattern_matches("sensor/FACE0003", "sensor/FACE0003/0")
    assert not _pattern_matches("actuator/FACE0003", "sensor/FACE0003/0")


def test_msg_to_source_keys():
    assert _msg_to_source_keys({"type": "sensor", "uid": "FACE0003",
                                 "channel_id": 0, "value": 1.0}) == ["sensor/FACE0003/0"]
    # No uid (e.g., raw schema-less probe) → wildcard slot.
    assert _msg_to_source_keys({"type": "sensor",
                                 "channel_id": 5, "value": 1.0}) == ["sensor/*/5"]
    assert _msg_to_source_keys({"type": "actuator_state",
                                 "uid": "FACE0002", "cmd": 1}) == ["actuator/FACE0002"]
    assert _msg_to_source_keys({"type": "hello"}) == []


def test_coarse_match_sensors_filter():
    t = OscTarget(id="x", host="h", port=1, sensors_filter=("imu",))
    assert _coarse_match(t, {"type": "sensor", "sensor": "imu", "slot": 3})
    assert not _coarse_match(t, {"type": "sensor", "sensor": "hr", "slot": 3})
    # Empty filter passes all sensor msgs.
    t2 = OscTarget(id="x", host="h", port=1)
    assert _coarse_match(t2, {"type": "sensor", "sensor": "anything"})


def test_coarse_match_actuators_gate():
    t_off = OscTarget(id="x", host="h", port=1, actuators_enabled=False)
    t_on = OscTarget(id="x", host="h", port=1, actuators_enabled=True)
    msg = {"type": "actuator_state", "slot": 2, "cmd": 1}
    assert not _coarse_match(t_off, msg)
    assert _coarse_match(t_on, msg)


_MINI_CATALOG = {
    "channels": {
        "AX":      {"id": 0,  "label": "ax"},
        "AY":      {"id": 1,  "label": "ay"},
        "AZ":      {"id": 2,  "label": "az"},
        "BPM":     {"id": 24, "label": "bpm"},
        "SPO2":    {"id": 25, "label": "spo2"},
        "LIGHT":   {"id": 41, "label": "light"},
    },
    "sensor_capabilities": {
        "imu":   ["AX", "AY", "AZ"],
        "hr":    ["BPM", "SPO2"],
        "light": ["LIGHT"],
    },
    "actuator_capabilities": {
        "led":       ["led"],
        "vibration": ["vib"],
    },
}


def test_schema_to_default_mappings():
    modules_by_uid = {"FACE0003": "imu_v2", "FACE0005": "hr_v1"}
    module_types_by_uid = {"FACE0003": "imu", "FACE0005": "hr"}
    rows = schema_to_default_mappings(modules_by_uid, module_types_by_uid,
                                       _MINI_CATALOG)
    addresses = {m.address for m in rows}
    sources = {m.source_pattern for m in rows}
    assert "/hex/imu/FACE0003/ax" in addresses
    assert "/hex/imu/FACE0003/az" in addresses
    assert "/hex/hr/FACE0005/spo2" in addresses
    assert "sensor/FACE0003/0" in sources
    assert "sensor/FACE0005/25" in sources
    assert len(rows) == 5
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
